btb/ClassicII/ClassicIIRevB/ClassicIIRevB.kicad_sch

## KiCad design ClassicIIRevB/ClassicIIRevB.kicad_sch (2026-08-08)

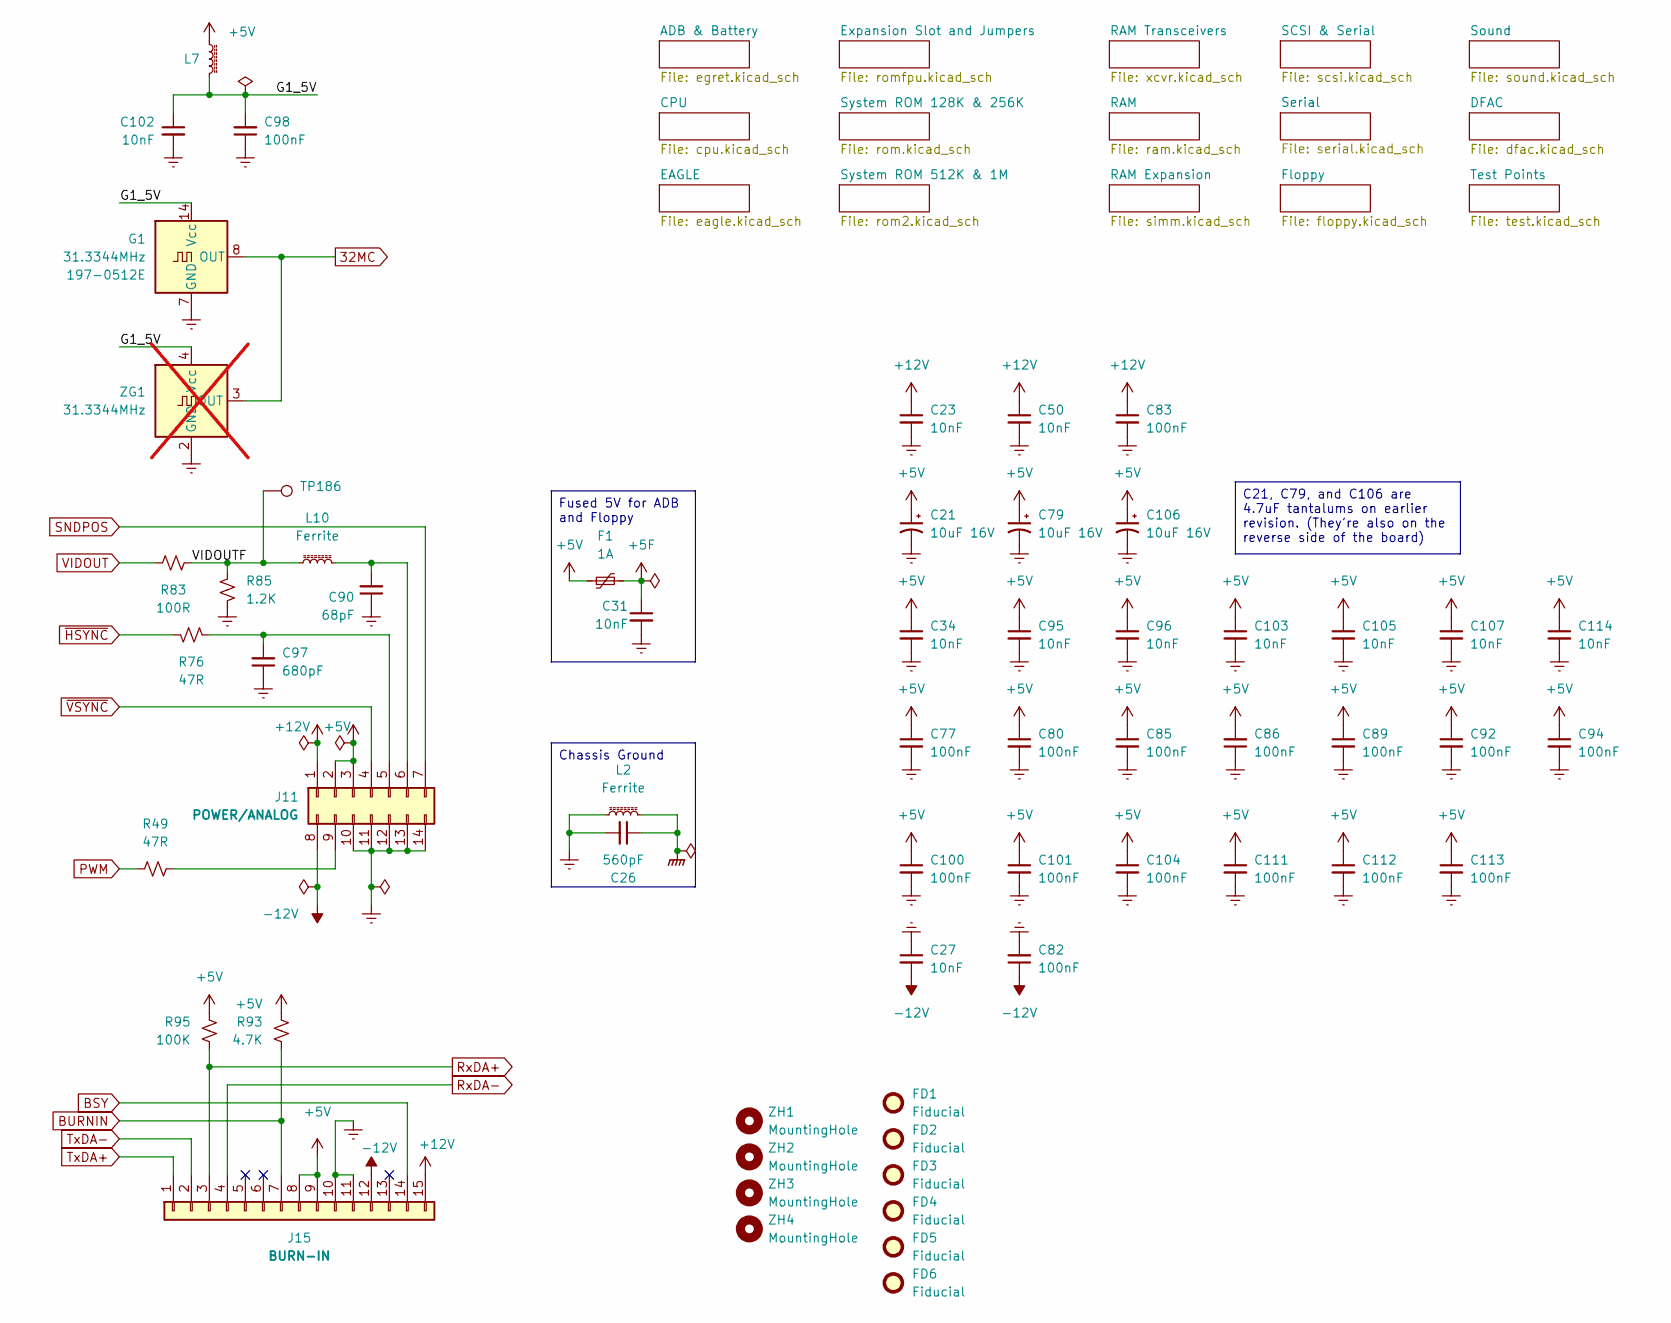
[picture p18: schematic ClassicIIRevB.kicad_sch]

Parts:
C21, C79, C106: 10uF 16V; CP_Elec_4x5.8
C23, C27, C31, C34, C50, C95, C96, C102, C103, C105, C107, C114: 10nF; SMD_0603_1608Metric_Pad1.52x1.02mm
C26: 560pF; SMD_0603_1608Metric_Pad1.52x1.02mm
C77, C80, C82, C83, C85, C86, C89, C92, C94, C98, C100, C101, C104, C113: 100nF; SMD_0603_1608Metric_Pad1.52x1.02mm
C90: 68pF; SMD_0603_1608Metric_Pad1.52x1.02mm
C97: 680pF; SMD_1206_3216Metric_Pad1.65x1.27mm
C111, C112: 100nF; SMD_0805_2012Metric_Pad1.25x1.65mm
F1: 1A; Fuse_2512_6332Metric_Pad2.54x2.54mm_HandSolder
FD1, FD6: Fiducial; Fiducial_1mm_Mask3mm_square
FD2, FD3, FD4, FD5: Fiducial; Fiducial_1mm_Mask3mm
G1: 31.3344MHz; Oscillator_DIP-14; PartNum 197-0512E
J11: POWER/ANALOG; Molex_Mini-Fit_Jr_5566-14A_2x07_P4.20mm_Vertical_RoundPads
J15: BURN-IN; Mac_Burn_In
L2, L7, L10: Ferrite; L_2010_5025Metric_Pad2.0x2.2mm_HandSolder
R49, R76: 47R; SMD_0805_2012Metric_Pad1.25x1.65mm
R83: 100R; SMD_0805_2012Metric_Pad1.25x1.65mm
R85: 1.2K; SMD_0805_2012Metric_Pad1.25x1.65mm
R93: 4.7K; SMD_0805_2012Metric_Pad1.25x1.65mm
R95: 100K; SMD_0805_2012Metric_Pad1.25x1.65mm
TP186: TestPoint_THTPad_D1.0mm_Drill0.5mm
ZG1: 31.3344MHz; Oscillator_SMD_Abracon_ABLNO; not fitted
ZH1, ZH2, ZH3, ZH4: MountingHole; MountingHole_3.2mm_M3_ISO14580

Connections:
32MC: G1.8 (OUT), ZG1.3 (OUT)
+5F: C31.1, F1.2
+5V: C21.1, C34.1, C77.1, C79.1, C80.1, C85.1, C86.2, C89.1, C92.1, C94.1, C95.1, C96.1, C100.1, C101.1, C103.1, C104.1, C105.1, C106.1, C107.1, C111.1, C112.1, C113.1, C114.1, F1.1, J11.2, J11.3, J15.8, J15.9, L7.2, R93.1, R95.1
+12V: C23.1, C50.1, C83.1, J11.1, J15.15
-12V: C27.2, C82.1, J11.8, J15.12
BSY: J15.14
BURNIN: J15.7, R93.2
G1_5V: C98.2, C102.1, G1.14 (Vcc), L7.1, ZG1.4 (Vcc)
GND: C21.2, C23.2, C26.2, C27.1, C31.2, C34.2, C50.2, C77.2, C79.2, C80.2, C82.2, C83.2, C85.2, C86.1, C89.2, C90.1, C92.2, C94.2, C95.2, C96.2, C97.1, C98.1, C100.2, C101.2, C102.2, C103.2, C104.2, C105.2, C106.2, C107.2, C111.2, C112.2, C113.2, C114.2, G1.7 (GND), J11.10, J11.11, J11.12, J11.13, J11.14, J15.10, J15.11, L2.1, R85.2, ZG1.2 (GND)
GNDPWR: C26.1, L2.2
unnamed: C90.2, J11.6, L10.2
unnamed: C97.2, J11.5, R76.2
unnamed: J11.9, R49.2
PWM: R49.1
RxDA+: J15.3, R95.2
RxDA-: J15.4
SNDPOS: J11.7
TxDA+: J15.1
TxDA-: J15.2
VIDOUT: R83.1
VIDOUTF: L10.1, R83.2, R85.1, TP186.1
~HSYNC: R76.1
~VSYNC: J11.4

Notes on the sheet:
Fused 5V for ADB and Floppy
Chassis Ground
C21, C79, and C106 are 4.7uF tantalums on earlier revision. (They're also on the reverse side of the board)
