btb/ClassicII/ClassicIIRevB/cpu.kicad_sch

## KiCad design ClassicIIRevB/cpu.kicad_sch (2026-08-08)

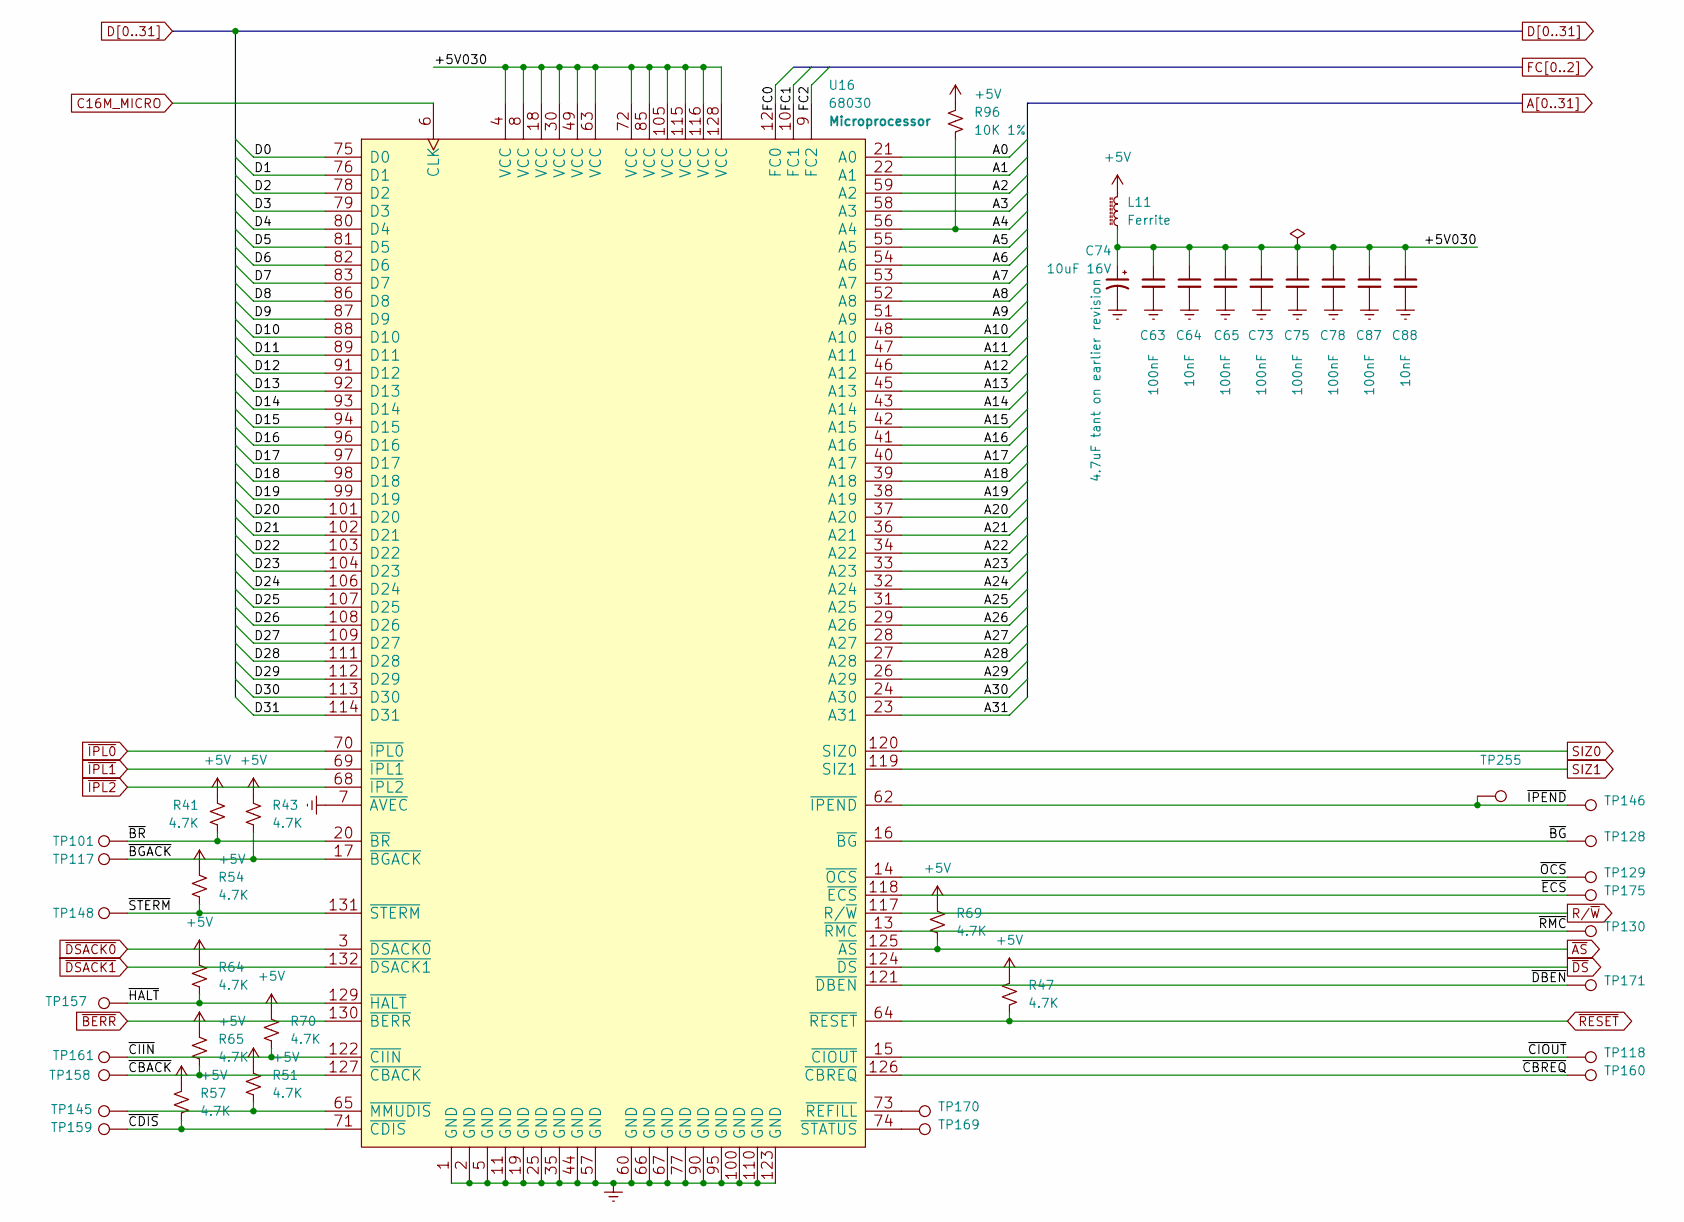
[picture p19: schematic cpu.kicad_sch]

Parts:
C63, C65, C73, C75, C78, C87: 100nF; SMD_0603_1608Metric_Pad1.52x1.02mm
C64, C88: 10nF; SMD_0603_1608Metric_Pad1.52x1.02mm
C74: 10uF 16V; CP_Elec_4x5.8
L11: Ferrite; L_2010_5025Metric_Pad2.0x2.2mm_HandSolder
R41, R43, R47, R51, R54, R57, R64, R65, R69, R70: 4.7K; SMD_0805_2012Metric_Pad1.25x1.65mm
R96: 10K 1%; SMD_0805_2012Metric_Pad1.25x1.65mm
TP101, TP117, TP118, TP128, TP129, TP130, TP145, TP146, TP148, TP159, TP169, TP170, TP171, TP255: TestPoint_THTPad_D1.0mm_Drill0.5mm
TP157, TP158, TP160, TP161, TP175: TestPoint_Pad_D1.0mm
U16: 68030; PQFP-132_24x24mm_P0.635mm_alt

Connections:
+5V: L11.1, R41.1, R43.1, R47.1, R51.1, R54.1, R57.1, R64.1, R65.1, R69.1, R70.1, R96.2
+5V030: C63.1, C64.1, C65.1, C73.1, C74.1, C75.1, C78.1, C87.1, C88.1, L11.2, U16.4 (VCC), U16.8 (VCC), U16.18 (VCC), U16.30 (VCC), U16.49 (VCC), U16.63 (VCC), U16.72 (VCC), U16.85 (VCC), U16.105 (VCC), U16.115 (VCC), U16.116 (VCC), U16.128 (VCC)
A0: U16.21 (A0)
A1: U16.22 (A1)
A2: U16.59 (A2)
A3: U16.58 (A3)
A4: R96.1, U16.56 (A4)
A5: U16.55 (A5)
A6: U16.54 (A6)
A7: U16.53 (A7)
A8: U16.52 (A8)
A9: U16.51 (A9)
A10: U16.48 (A10)
A11: U16.47 (A11)
A12: U16.46 (A12)
A13: U16.45 (A13)
A14: U16.43 (A14)
A15: U16.42 (A15)
A16: U16.41 (A16)
A17: U16.40 (A17)
A18: U16.39 (A18)
A19: U16.38 (A19)
A20: U16.37 (A20)
A21: U16.36 (A21)
A22: U16.34 (A22)
A23: U16.33 (A23)
A24: U16.32 (A24)
A25: U16.31 (A25)
A26: U16.29 (A26)
A27: U16.28 (A27)
A28: U16.27 (A28)
A29: U16.26 (A29)
A30: U16.24 (A30)
A31: U16.23 (A31)
C16M_MICRO: U16.6 (CLK)
D0: U16.75 (D0)
D1: U16.76 (D1)
D2: U16.78 (D2)
D3: U16.79 (D3)
D4: U16.80 (D4)
D5: U16.81 (D5)
D6: U16.82 (D6)
D7: U16.83 (D7)
D8: U16.86 (D8)
D9: U16.87 (D9)
D10: U16.88 (D10)
D11: U16.89 (D11)
D12: U16.91 (D12)
D13: U16.92 (D13)
D14: U16.93 (D14)
D15: U16.94 (D15)
D16: U16.96 (D16)
D17: U16.97 (D17)
D18: U16.98 (D18)
D19: U16.99 (D19)
D20: U16.101 (D20)
D21: U16.102 (D21)
D22: U16.103 (D22)
D23: U16.104 (D23)
D24: U16.106 (D24)
D25: U16.107 (D25)
D26: U16.108 (D26)
D27: U16.109 (D27)
D28: U16.111 (D28)
D29: U16.112 (D29)
D30: U16.113 (D30)
D31: U16.114 (D31)
FC0: U16.12 (FC0)
FC1: U16.10 (FC1)
FC2: U16.9 (FC2)
GND: C63.2, C64.2, C65.2, C73.2, C74.2, C75.2, C78.2, C87.2, C88.2, U16.1 (GND), U16.2 (GND), U16.5 (GND), U16.7 (~AVEC), U16.11 (GND), U16.19 (GND), U16.25 (GND), U16.35 (GND), U16.44 (GND), U16.57 (GND), U16.60 (GND), U16.66 (GND), U16.67 (GND), U16.77 (GND), U16.90 (GND), U16.95 (GND), U16.100 (GND), U16.110 (GND), U16.123 (GND)
unnamed: R51.2, TP145.1, U16.65 (~MMUDIS)
unnamed: TP169.1, U16.74 (~STATUS)
unnamed: TP170.1, U16.73 (~REFILL)
R/~W: U16.117 (R/~W)
SIZ0: U16.120 (SIZ0)
SIZ1: U16.119 (SIZ1)
~AS: R69.2, U16.125 (~AS)
~BERR: U16.130 (~BERR)
~BGACK: R43.2, TP117.1, U16.17 (~BGACK)
~BG: TP128.1, U16.16 (~BG)
~BR: R41.2, TP101.1, U16.20 (~BR)
~CBACK: R65.2, TP158.1, U16.127 (~CBACK)
~CBREQ: TP160.1, U16.126 (~CBREQ)
~CDIS: R57.2, TP159.1, U16.71 (~CDIS)
~CIIN: R70.2, TP161.1, U16.122 (~CIIN)
~CIOUT: TP118.1, U16.15 (~CIOUT)
~DBEN: TP171.1, U16.121 (~DBEN)
~DSACK0: U16.3 (~DSACK0)
~DSACK1: U16.132 (~DSACK1)
~DS: U16.124 (~DS)
~ECS: TP175.1, U16.118 (~ECS)
~HALT: R64.2, TP157.1, U16.129 (~HALT)
~IPEND: TP146.1, TP255.1, U16.62 (~IPEND)
~IPL0: U16.70 (~IPL0)
~IPL1: U16.69 (~IPL1)
~IPL2: U16.68 (~IPL2)
~OCS: TP129.1, U16.14 (~OCS)
~RESET: R47.2, U16.64 (~RESET)
~RMC: TP130.1, U16.13 (~RMC)
~STERM: R54.2, TP148.1, U16.131 (~STERM)
