btb/ClassicII/ClassicIIRevB/dfac.kicad_sch

## KiCad design ClassicIIRevB/dfac.kicad_sch (2026-08-08)

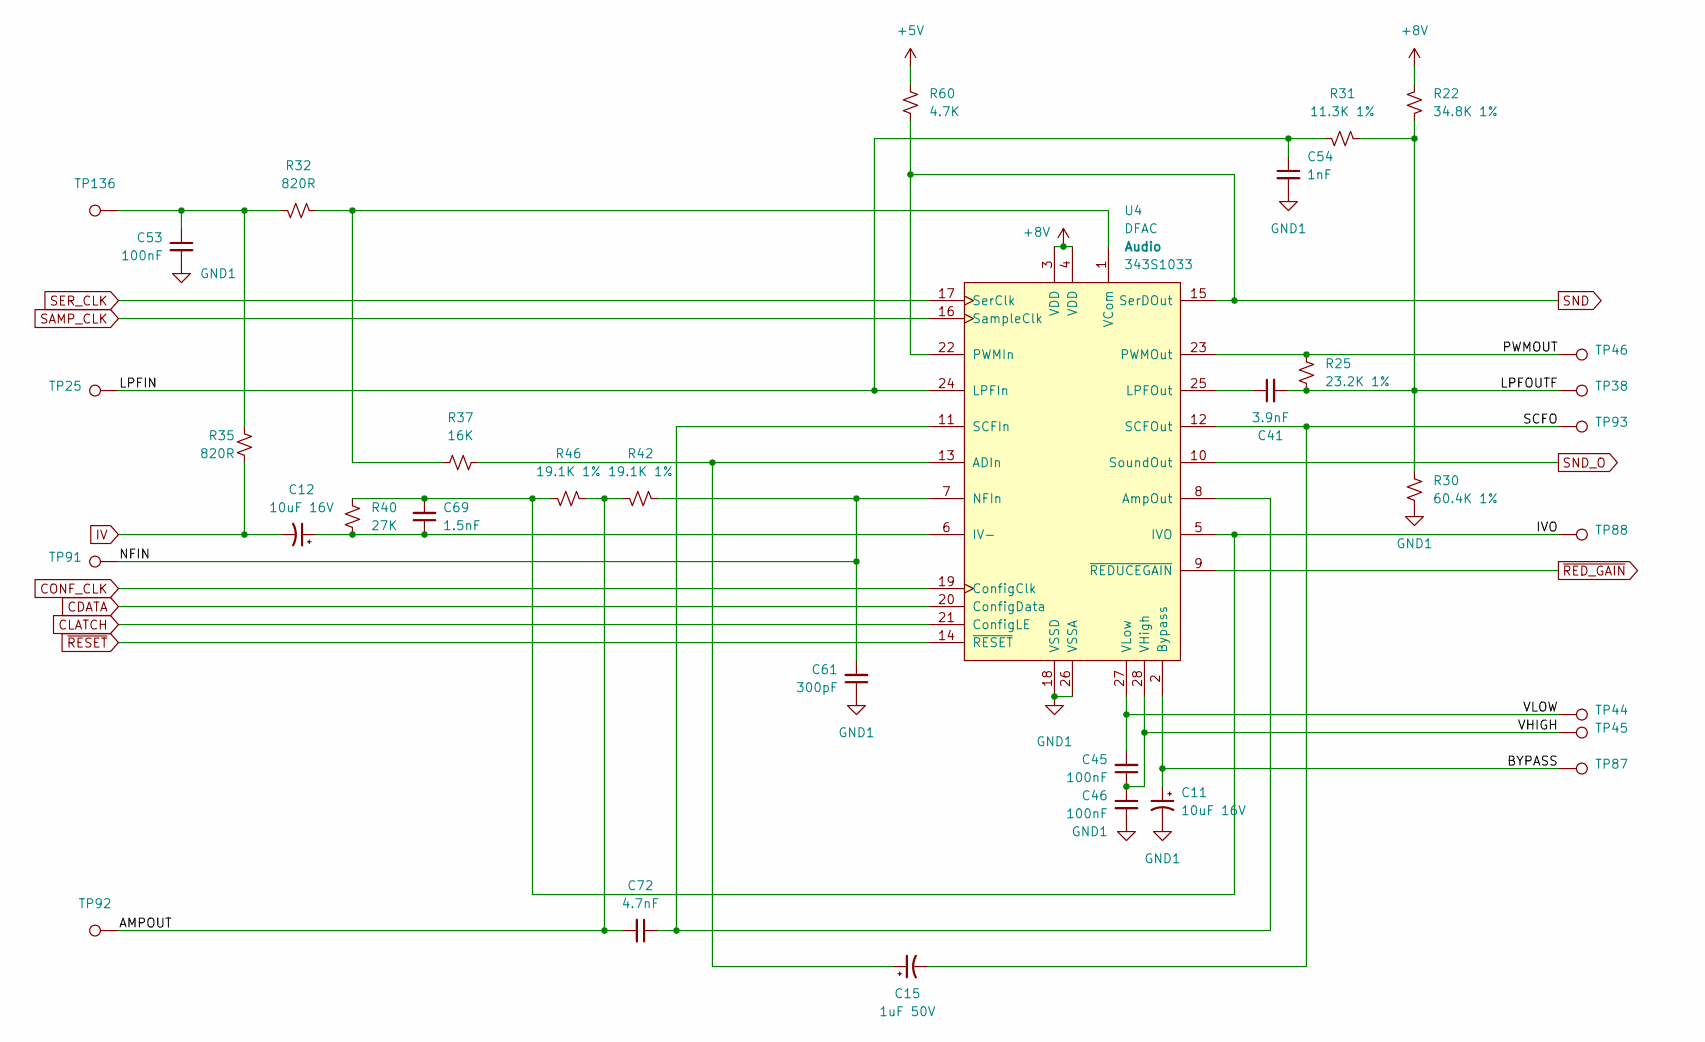
[picture p20: schematic dfac.kicad_sch]

Parts:
C11, C12: 10uF 16V; CP_Elec_4x5.8
C15: 1uF 50V; CP_Elec_4x5.8
C41: 3.9nF; SMD_0603_1608Metric_Pad1.52x1.02mm
C45, C46, C53: 100nF; SMD_0603_1608Metric_Pad1.52x1.02mm
C54: 1nF; SMD_0603_1608Metric_Pad1.52x1.02mm
C61: 300pF; SMD_1206_3216Metric_Pad1.65x1.27mm
C69: 1.5nF; SMD_0805_2012Metric_Pad1.25x1.65mm
C72: 4.7nF; SMD_0603_1608Metric_Pad1.52x1.02mm
R22: 34.8K 1%; SMD_0805_2012Metric_Pad1.25x1.65mm
R25: 23.2K 1%; SMD_0805_2012Metric_Pad1.25x1.65mm
R30: 60.4K 1%; SMD_0805_2012Metric_Pad1.25x1.65mm
R31: 11.3K 1%; SMD_0805_2012Metric_Pad1.25x1.65mm
R32, R35: 820R; SMD_0805_2012Metric_Pad1.25x1.65mm
R37: 16K; SMD_0805_2012Metric_Pad1.25x1.65mm
R40: 27K; SMD_0805_2012Metric_Pad1.25x1.65mm
R42, R46: 19.1K 1%; SMD_0805_2012Metric_Pad1.25x1.65mm
R60: 4.7K; SMD_0805_2012Metric_Pad1.25x1.65mm
TP25, TP44, TP87, TP93: TestPoint_THTPad_D1.0mm_Drill0.5mm
TP38, TP45, TP46, TP88, TP91, TP92, TP136: TestPoint_Pad_D1.0mm
U4: DFAC; PLCC-28_rounded; PartNum 343S1033

Connections:
+5V: R60.1
+8V: R22.1, U4.3 (VDD), U4.4 (VDD)
AMPOUT: C72.2, R42.1, R46.1, TP92.1
BYPASS: C11.1, TP87.1, U4.2 (Bypass)
CDATA: U4.20 (ConfigData)
CLATCH: U4.21 (ConfigLE)
CONF_CLK: U4.19 (ConfigClk)
GND1: C11.2, C46.2, C53.2, C54.2, C61.1, R30.1, U4.18 (VSSD), U4.26 (VSSA)
IV: C12.2, R35.1
IVO: C69.2, R40.1, R46.2, TP88.1, U4.5 (IVO)
LPFIN: C54.1, R31.2, TP25.1, U4.24 (LPFIn)
LPFOUTF: C41.2, R22.2, R25.1, R30.2, R31.1, TP38.1
NFIN: C61.2, R42.2, TP91.1, U4.7 (NFIn)
unnamed: C12.1, C69.1, R40.2, U4.6 (IV-)
unnamed: C15.1, R37.1, U4.13 (ADIn)
unnamed: C41.1, U4.25 (LPFOut)
unnamed: C53.1, R32.1, R35.2, TP136.1
unnamed: C72.1, U4.8 (AmpOut), U4.11 (SCFIn)
unnamed: R32.2, R37.2, U4.1 (VCom)
PWMOUT: R25.2, TP46.1, U4.23 (PWMOut)
SAMP_CLK: U4.16 (SampleClk)
SCFO: C15.2, TP93.1, U4.12 (SCFOut)
SER_CLK: U4.17 (SerClk)
SND: R60.2, U4.15 (SerDOut), U4.22 (PWMIn)
SND_O: U4.10 (SoundOut)
VHIGH: C45.1, C46.1, TP45.1, U4.28 (VHigh)
VLOW: C45.2, TP44.1, U4.27 (VLow)
~RED_GAIN: U4.9 (~REDUCEGAIN)
~RESET: U4.14 (~RESET)
