btb/ClassicII/ClassicIIRevB/eagle.kicad_sch

## KiCad design ClassicIIRevB/eagle.kicad_sch (2026-08-08)

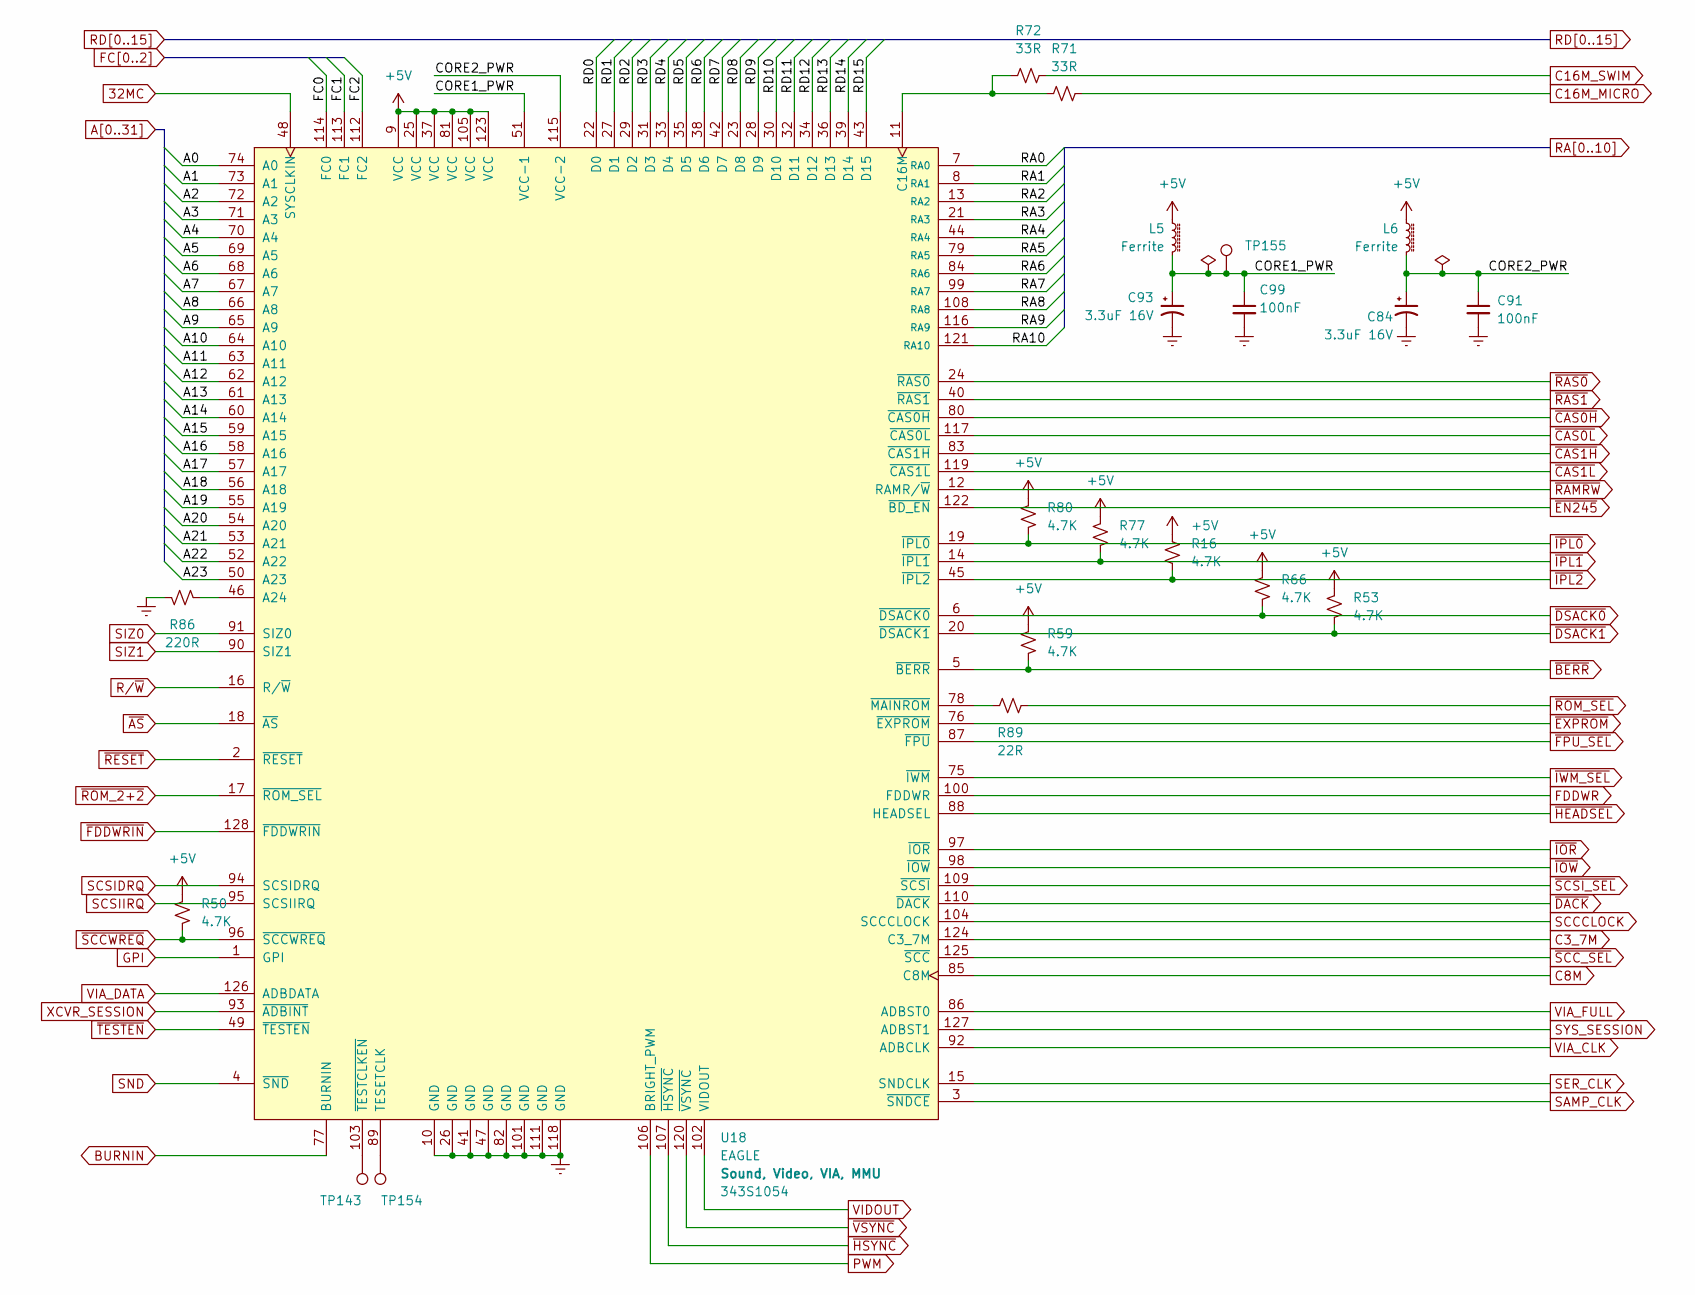
[picture p21: schematic eagle.kicad_sch]

Parts:
C84, C93: 3.3uF 16V; CP_EIA-3528-21_Kemet-B_Pad3.0x2.35mm_HandSolder
C91, C99: 100nF; SMD_0603_1608Metric_Pad1.52x1.02mm
L5, L6: Ferrite; L_2010_5025Metric_Pad2.0x2.2mm_HandSolder
R16, R50, R53, R59, R66, R77, R80: 4.7K; SMD_0805_2012Metric_Pad1.25x1.65mm
R71, R72: 33R; SMD_0805_2012Metric_Pad1.25x1.65mm
R86: 220R; SMD_0805_2012Metric_Pad1.25x1.65mm
R89: 22R; SMD_0805_2012Metric_Pad1.25x1.65mm
TP143, TP154, TP155: TestPoint_THTPad_D1.0mm_Drill0.5mm
U18: EAGLE; TQFP-128_28x28mm_P0.8mm; PartNum 343S1054

Connections:
32MC: U18.48 (SYSCLKIN)
+5V: L5.1, L6.1, R16.1, R50.1, R53.1, R59.1, R66.1, R77.2, R80.1, U18.9 (VCC), U18.25 (VCC), U18.37 (VCC), U18.81 (VCC), U18.105 (VCC), U18.123 (VCC)
A0: U18.74 (A0)
A1: U18.73 (A1)
A2: U18.72 (A2)
A3: U18.71 (A3)
A4: U18.70 (A4)
A5: U18.69 (A5)
A6: U18.68 (A6)
A7: U18.67 (A7)
A8: U18.66 (A8)
A9: U18.65 (A9)
A10: U18.64 (A10)
A11: U18.63 (A11)
A12: U18.62 (A12)
A13: U18.61 (A13)
A14: U18.60 (A14)
A15: U18.59 (A15)
A16: U18.58 (A16)
A17: U18.57 (A17)
A18: U18.56 (A18)
A19: U18.55 (A19)
A20: U18.54 (A20)
A21: U18.53 (A21)
A22: U18.52 (A22)
A23: U18.50 (A23)
BURNIN: U18.77 (BURNIN)
C3_7M: U18.124 (C3_7M)
C8M: U18.85 (C8M)
C16M_MICRO: R71.1
C16M_SWIM: R72.1
CORE1_PWR: C93.1, C99.1, L5.2, TP155.1, U18.51 (VCC-1)
CORE2_PWR: C84.1, C91.1, L6.2, U18.115 (VCC-2)
FC0: U18.114 (FC0)
FC1: U18.113 (FC1)
FC2: U18.112 (FC2)
FDDWR: U18.100 (FDDWR)
GND: C84.2, C91.2, C93.2, C99.2, R86.1, U18.10 (GND), U18.26 (GND), U18.41 (GND), U18.47 (GND), U18.82 (GND), U18.101 (GND), U18.111 (GND), U18.118 (GND)
GPI: U18.1 (GPI)
unnamed: R71.2, R72.2, U18.11 (C16M)
unnamed: R86.2, U18.46 (A24)
unnamed: R89.1, U18.78 (~MAINROM)
unnamed: TP143.1, U18.103 (~TESTCLKEN)
unnamed: TP154.1, U18.89 (TESETCLK)
PWM: U18.106 (BRIGHT_PWM)
RA0: U18.7 (RA0)
RA1: U18.8 (RA1)
RA2: U18.13 (RA2)
RA3: U18.21 (RA3)
RA4: U18.44 (RA4)
RA5: U18.79 (RA5)
RA6: U18.84 (RA6)
RA7: U18.99 (RA7)
RA8: U18.108 (RA8)
RA9: U18.116 (RA9)
RA10: U18.121 (RA10)
RD0: U18.22 (D0)
RD1: U18.27 (D1)
RD2: U18.29 (D2)
RD3: U18.31 (D3)
RD4: U18.33 (D4)
RD5: U18.35 (D5)
RD6: U18.38 (D6)
RD7: U18.42 (D7)
RD8: U18.23 (D8)
RD9: U18.28 (D9)
RD10: U18.30 (D10)
RD11: U18.32 (D11)
RD12: U18.34 (D12)
RD13: U18.36 (D13)
RD14: U18.39 (D14)
RD15: U18.43 (D15)
R/~W: U18.16 (R/~W)
SAMP_CLK: U18.3 (~SNDCE)
SCCCLOCK: U18.104 (SCCCLOCK)
SCSIDRQ: U18.94 (SCSIDRQ)
SCSIIRQ: U18.95 (SCSIIRQ)
SER_CLK: U18.15 (SNDCLK)
SIZ0: U18.91 (SIZ0)
SIZ1: U18.90 (SIZ1)
SND: U18.4 (~SND)
SYS_SESSION: U18.127 (ADBST1)
VIA_CLK: U18.92 (ADBCLK)
VIA_DATA: U18.126 (ADBDATA)
VIA_FULL: U18.86 (ADBST0)
VIDOUT: U18.102 (VIDOUT)
XCVR_SESSION: U18.93 (~ADBINT)
~AS: U18.18 (~AS)
~BERR: R59.2, U18.5 (~BERR)
~CAS0H: U18.80 (~CAS0H)
~CAS0L: U18.117 (~CAS0L)
~CAS1H: U18.83 (~CAS1H)
~CAS1L: U18.119 (~CAS1L)
~DACK: U18.110 (~DACK)
~DSACK0: R66.2, U18.6 (~DSACK0)
~DSACK1: R53.2, U18.20 (~DSACK1)
~EN245: U18.122 (~BD_EN)
~EXPROM: U18.76 (~EXPROM)
~FDDWRIN: U18.128 (~FDDWRIN)
~FPU_SEL: U18.87 (~FPU)
~HEADSEL: U18.88 (HEADSEL)
~HSYNC: U18.107 (~HSYNC)
~IOR: U18.97 (~IOR)
~IOW: U18.98 (~IOW)
~IPL0: R80.2, U18.19 (~IPL0)
~IPL1: R77.1, U18.14 (~IPL1)
~IPL2: R16.2, U18.45 (~IPL2)
~IWM_SEL: U18.75 (~IWM)
~RAMRW: U18.12 (RAMR/~W)
~RAS0: U18.24 (~RAS0)
~RAS1: U18.40 (~RAS1)
~RESET: U18.2 (~RESET)
~ROM_2+2: U18.17 (~ROM_SEL)
~ROM_SEL: R89.2
~SCCWREQ: R50.2, U18.96 (~SCCWREQ)
~SCC_SEL: U18.125 (~SCC)
~SCSI_SEL: U18.109 (~SCSI)
~TESTEN: U18.49 (~TESTEN)
~VSYNC: U18.120 (~VSYNC)
