btb/ClassicII/ClassicIIRevB/egret.kicad_sch

## KiCad design ClassicIIRevB/egret.kicad_sch (2026-08-08)

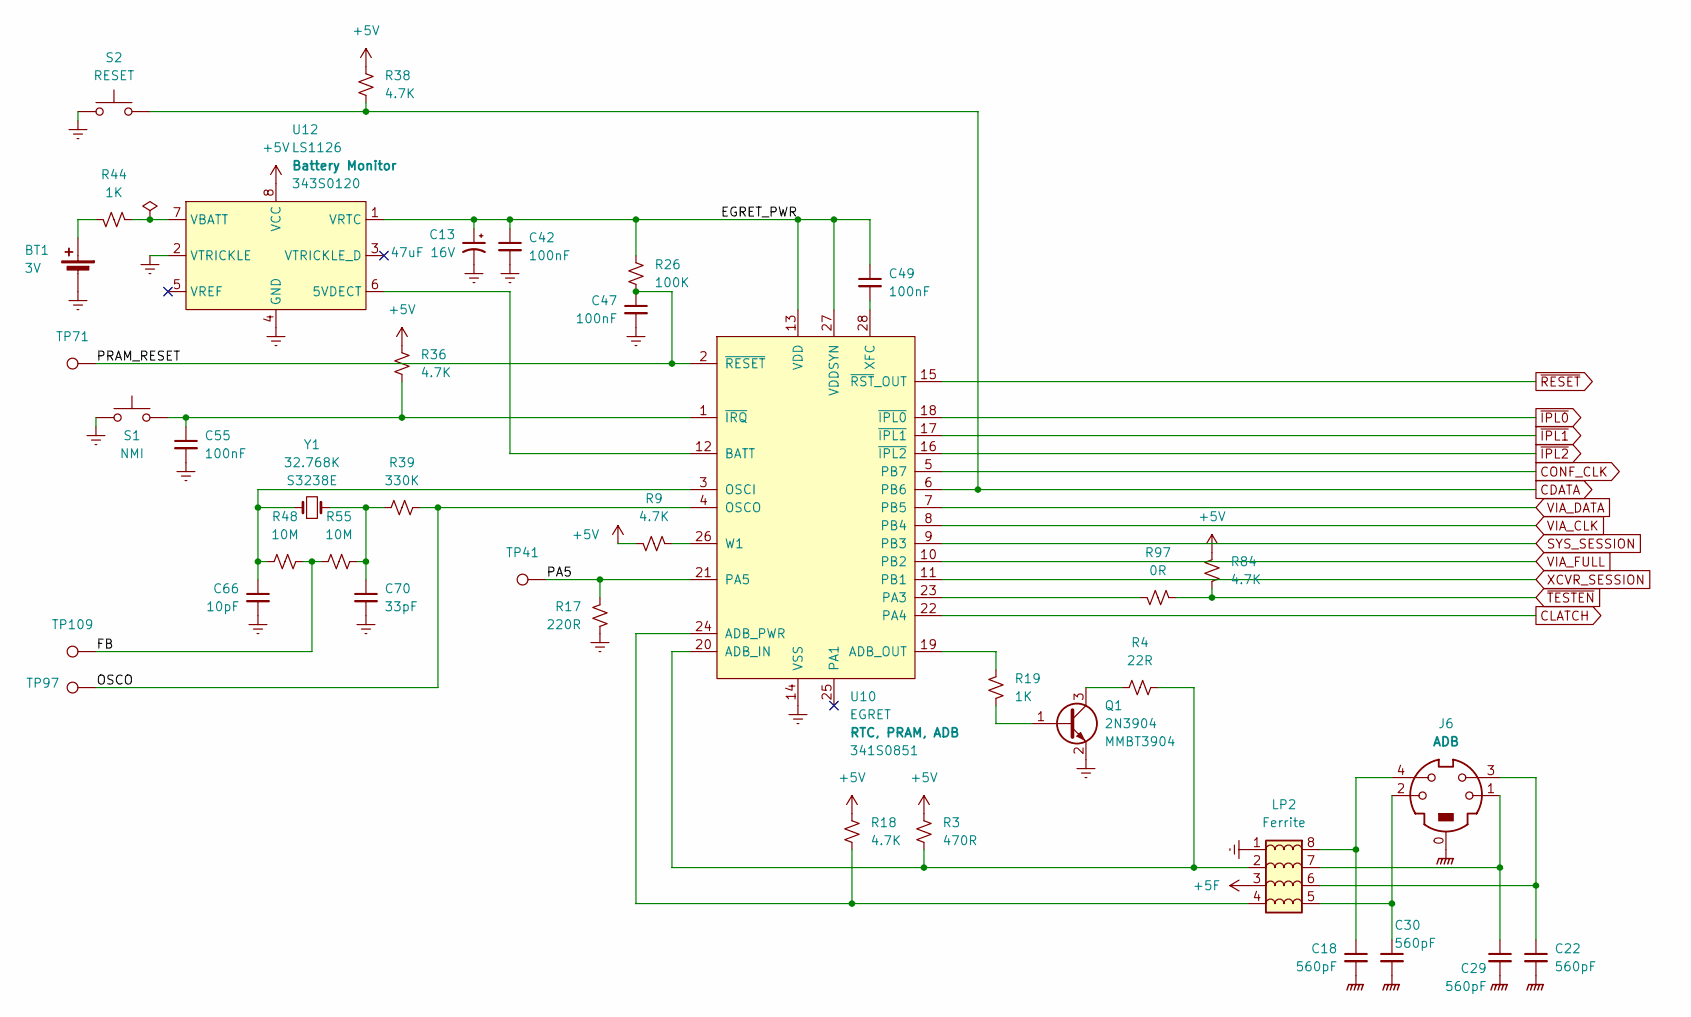
[picture p22: schematic egret.kicad_sch]

Parts:
BT1: 3V; BatteryHolder_Keystone_108_1_2xAA
C13: 47uF 16V; CP_Elec_6.3x5.4
C18, C22, C29, C30: 560pF; SMD_0603_1608Metric_Pad1.52x1.02mm
C42, C47, C49, C55: 100nF; SMD_0603_1608Metric_Pad1.52x1.02mm
C66: 10pF; SMD_0603_1608Metric_Pad1.52x1.02mm
C70: 33pF; SMD_0603_1608Metric_Pad1.52x1.02mm
J6: ADB; TE_5749263-1_MINI_DIN_4_RA_Shield
LP2: Ferrite; L_Pack04_P2.54mm
Q1: 2N3904; SOT-23_Handsoldering; PartNum MMBT3904
R3: 470R; SMD_0805_2012Metric_Pad1.25x1.65mm
R4: 22R; SMD_0805_2012Metric_Pad1.25x1.65mm
R9, R18, R36, R38, R84: 4.7K; SMD_0805_2012Metric_Pad1.25x1.65mm
R17: 220R; SMD_0805_2012Metric_Pad1.25x1.65mm
R19, R44: 1K; SMD_0805_2012Metric_Pad1.25x1.65mm
R26: 100K; SMD_0805_2012Metric_Pad1.25x1.65mm
R39: 330K; SMD_0805_2012Metric_Pad1.25x1.65mm
R48, R55: 10M; SMD_0805_2012Metric_Pad1.25x1.65mm
R97: 0R; SMD_0805_2012Metric_Pad1.25x1.65mm
S1: NMI; SW_SPST_Omron_B3F_angled
S2: RESET; SW_SPST_Omron_B3F_angled
TP41, TP71, TP109: TestPoint_THTPad_D1.0mm_Drill0.5mm
TP97: TestPoint_Pad_D1.0mm
U10: EGRET; SOIC-28W_7.5x17.9mm_P1.27mm_oval; PartNum 341S0851
U12: LS1126; SOIC-8_3.9x4.9mm_P1.27mm_oval; PartNum 343S0120
Y1: 32.768K; Crystal_AT310_D3.0mm_L10.0mm_Vertical; PartNum S3238E

Connections:
+5F: LP2.3
+5V: R3.1, R9.1, R18.1, R36.1, R38.1, R84.1, U12.8 (VCC)
CDATA: R38.2, S2.2, U10.6 (PB6)
CLATCH: U10.22 (PA4)
CONF_CLK: U10.5 (PB7)
EGRET_PWR: C13.1, C42.1, C49.1, R26.1, U10.13 (VDD), U10.27 (VDDSYN), U12.1 (VRTC)
FB: R48.2, R55.1, TP109.1
GND: BT1.2 (-), C13.2, C42.2, C47.2, C55.2, C66.2, C70.2, LP2.1, Q1.2 (E), R17.2, S1.1, S2.1, U10.14 (VSS), U12.2 (VTRICKLE), U12.4 (GND)
GNDPWR: C18.2, C22.2, C29.2, C30.2, J6.0
unnamed: BT1.1 (+), R44.1
unnamed: C18.1, J6.4, LP2.8
unnamed: C22.1, J6.3, LP2.6
unnamed: C29.1, J6.1, LP2.7
unnamed: C30.1, J6.2, LP2.5
unnamed: C49.2, U10.28 (XFC)
unnamed: C55.1, R36.2, S1.2, U10.1 (~IRQ)
unnamed: C66.1, R48.1, U10.3 (OSCI), Y1.1
unnamed: C70.1, R39.1, R55.2, Y1.2
unnamed: LP2.2, R3.2, R4.1, U10.20 (ADB_IN)
unnamed: LP2.4, R18.2, U10.24 (ADB_PWR)
unnamed: Q1.1 (B), R19.2
unnamed: Q1.3 (C), R4.2
unnamed: R9.2, U10.26 (W1)
unnamed: R19.1, U10.19 (ADB_OUT)
unnamed: R44.2, U12.7 (VBATT)
unnamed: R97.1, U10.23 (PA3)
unnamed: U10.12 (BATT), U12.6 (5VDECT)
OSCO: R39.2, TP97.1, U10.4 (OSCO)
PA5: R17.1, TP41.1, U10.21 (PA5)
PRAM_RESET: C47.1, R26.2, TP71.1, U10.2 (~RESET)
SYS_SESSION: U10.9 (PB3)
VIA_CLK: U10.8 (PB4)
VIA_DATA: U10.7 (PB5)
VIA_FULL: U10.10 (PB2)
XCVR_SESSION: U10.11 (PB1)
~IPL0: U10.18 (~IPL0)
~IPL1: U10.17 (~IPL1)
~IPL2: U10.16 (~IPL2)
~RESET: U10.15 (~RST_OUT)
~TESTEN: R84.2, R97.2
