btb/ClassicII/ClassicIIRevB/floppy.kicad_sch

## KiCad design ClassicIIRevB/floppy.kicad_sch (2026-08-08)

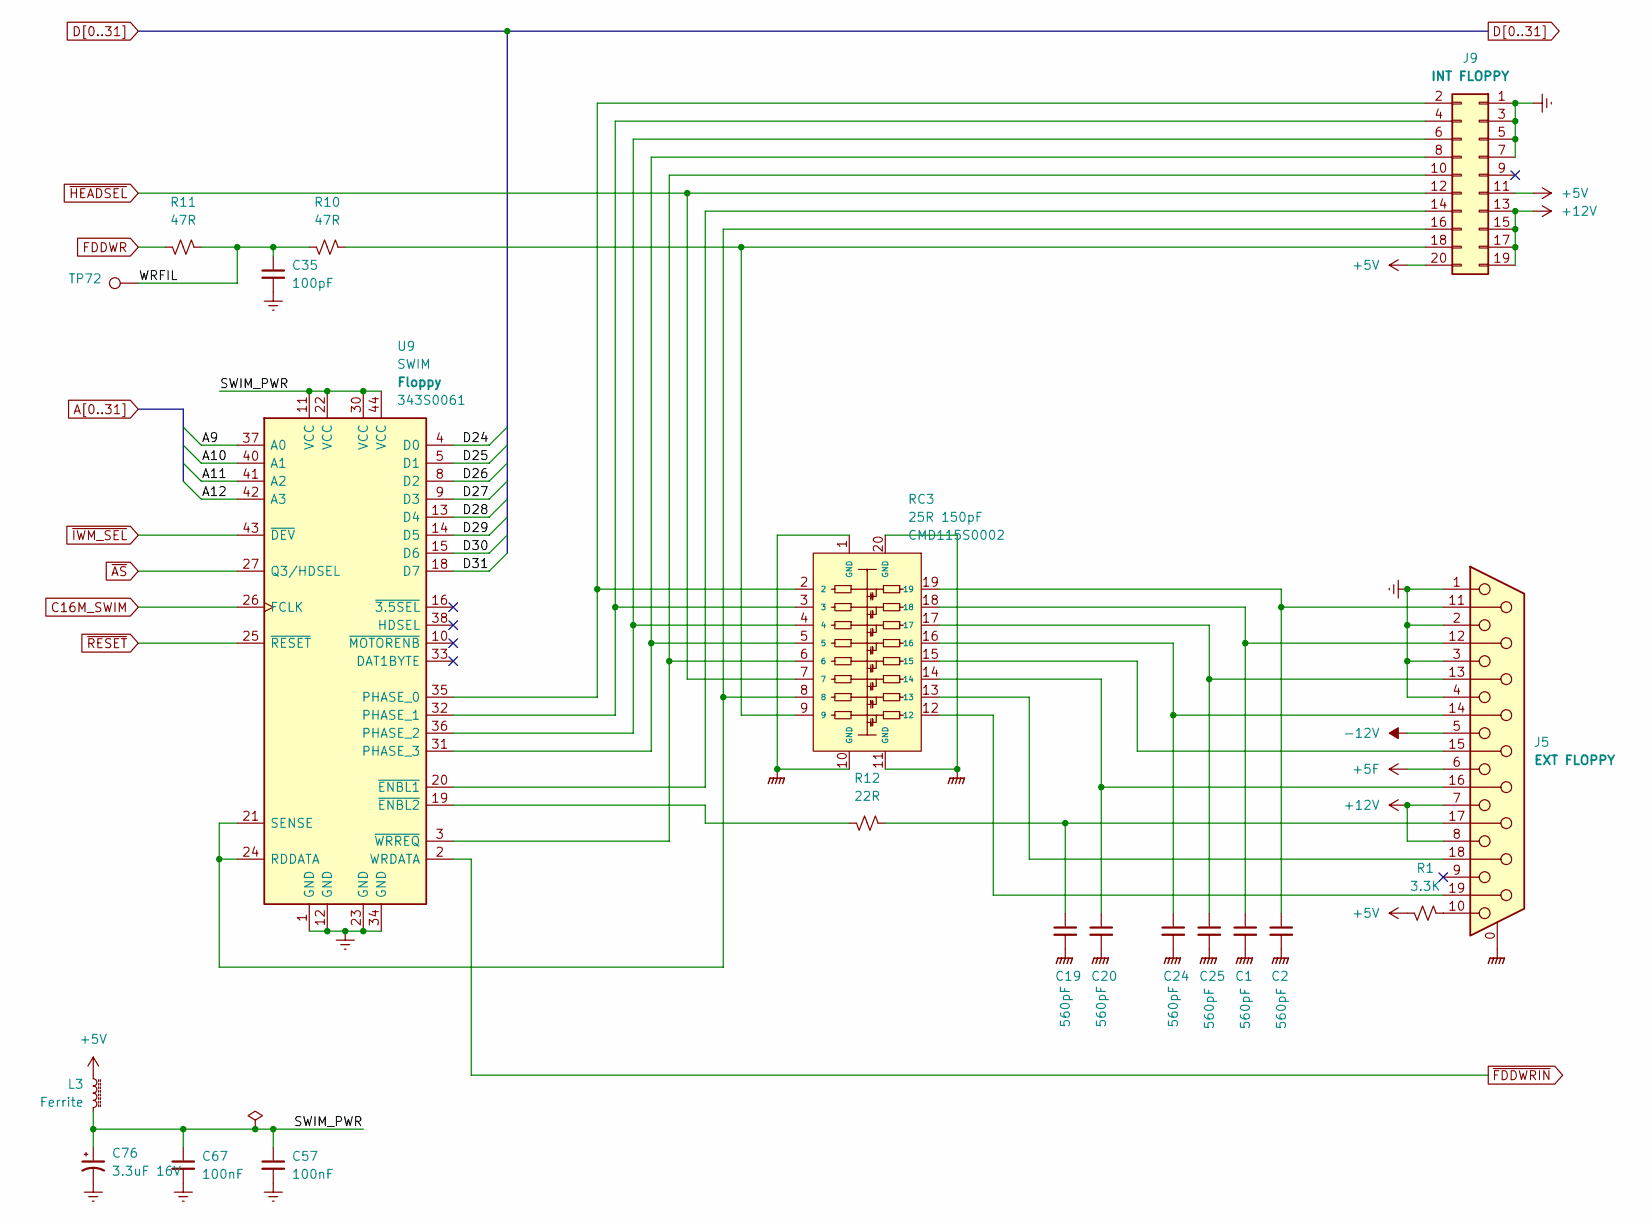
[picture p23: schematic floppy.kicad_sch]

Parts:
C1, C2, C19, C20, C24, C25: 560pF; SMD_0603_1608Metric_Pad1.52x1.02mm
C35: 100pF; SMD_0603_1608Metric_Pad1.52x1.02mm
C57, C67: 100nF; SMD_0603_1608Metric_Pad1.52x1.02mm
C76: 3.3uF 16V; CP_EIA-3528-21_Kemet-B_Pad3.0x2.35mm_HandSolder
J5: EXT FLOPPY; DSUB-19_Female_Horizontal_P2.77x2.84mm_EdgePinOffset4.94mm_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
J9: INT FLOPPY; IDC-Header_2x10_P2.54mm_Vertical
L3: Ferrite; L_2010_5025Metric_Pad2.0x2.2mm_HandSolder
R1: 3.3K; SMD_0805_2012Metric_Pad1.25x1.65mm
R10, R11: 47R; SMD_0805_2012Metric_Pad1.25x1.65mm
R12: 22R; SMD_0805_2012Metric_Pad1.25x1.65mm
RC3: 25R 150pF; SOIC-20W_7.5x12.8mm_P1.27mm_oval; PartNum CMD115S0002
TP72: TestPoint_Pad_D1.0mm
U9: SWIM; PLCC-44_16.6x16.6mm_P1.27mm_oval; PartNum 343S0061

Connections:
+5F: J5.6
+5V: J9.11, J9.20, L3.2, R1.1
+12V: J5.7, J5.8, J9.13, J9.15, J9.17, J9.19
-12V: J5.5
A9: U9.37 (A0)
A10: U9.40 (A1)
A11: U9.41 (A2)
A12: U9.42 (A3)
C16M_SWIM: U9.26 (FCLK)
D24: U9.4 (D0)
D25: U9.5 (D1)
D26: U9.8 (D2)
D27: U9.9 (D3)
D28: U9.13 (D4)
D29: U9.14 (D5)
D30: U9.15 (D6)
D31: U9.18 (D7)
FDDWR: R11.1
GND: C35.2, C57.2, C67.2, C76.2, J5.1, J5.2, J5.3, J5.4, J9.1, J9.3, J9.5, J9.7, U9.1 (GND), U9.12 (GND), U9.23 (GND), U9.34 (GND)
GNDPWR: C1.2, C2.2, C19.2, C20.2, C24.2, C25.2, J5.0 (PAD), RC3.1 (GND), RC3.10 (GND), RC3.11 (GND), RC3.20 (GND)
unnamed: C1.1, J5.12, RC3.18
unnamed: C2.1, J5.11, RC3.19
unnamed: C19.1, J5.17, R12.1
unnamed: C20.1, J5.16, RC3.14
unnamed: C24.1, J5.14, RC3.16
unnamed: C25.1, J5.13, RC3.17
unnamed: J5.10, R1.2
unnamed: J5.15, RC3.15
unnamed: J5.18, RC3.13
unnamed: J5.19, RC3.12
unnamed: J9.2, RC3.2, U9.35 (PHASE_0)
unnamed: J9.4, RC3.3, U9.32 (PHASE_1)
unnamed: J9.6, RC3.4, U9.36 (PHASE_2)
unnamed: J9.8, RC3.5, U9.31 (PHASE_3)
unnamed: J9.10, RC3.6, U9.3 (~WRREQ)
unnamed: J9.14, U9.20 (~ENBL1)
unnamed: J9.16, RC3.8, U9.21 (SENSE), U9.24 (RDDATA)
unnamed: J9.18, R10.2, RC3.9
unnamed: R12.2, U9.19 (~ENBL2)
SWIM_PWR: C57.1, C67.1, C76.1, L3.1, U9.11 (VCC), U9.22 (VCC), U9.30 (VCC), U9.44 (VCC)
WRFIL: C35.1, R10.1, R11.2, TP72.1
~AS: U9.27 (Q3/HDSEL)
~FDDWRIN: U9.2 (WRDATA)
~HEADSEL: J9.12, RC3.7
~IWM_SEL: U9.43 (~DEV)
~RESET: U9.25 (~RESET)
