btb/ClassicII/ClassicIIRevB/ram.kicad_sch

## KiCad design ClassicIIRevB/ram.kicad_sch (2026-08-08)

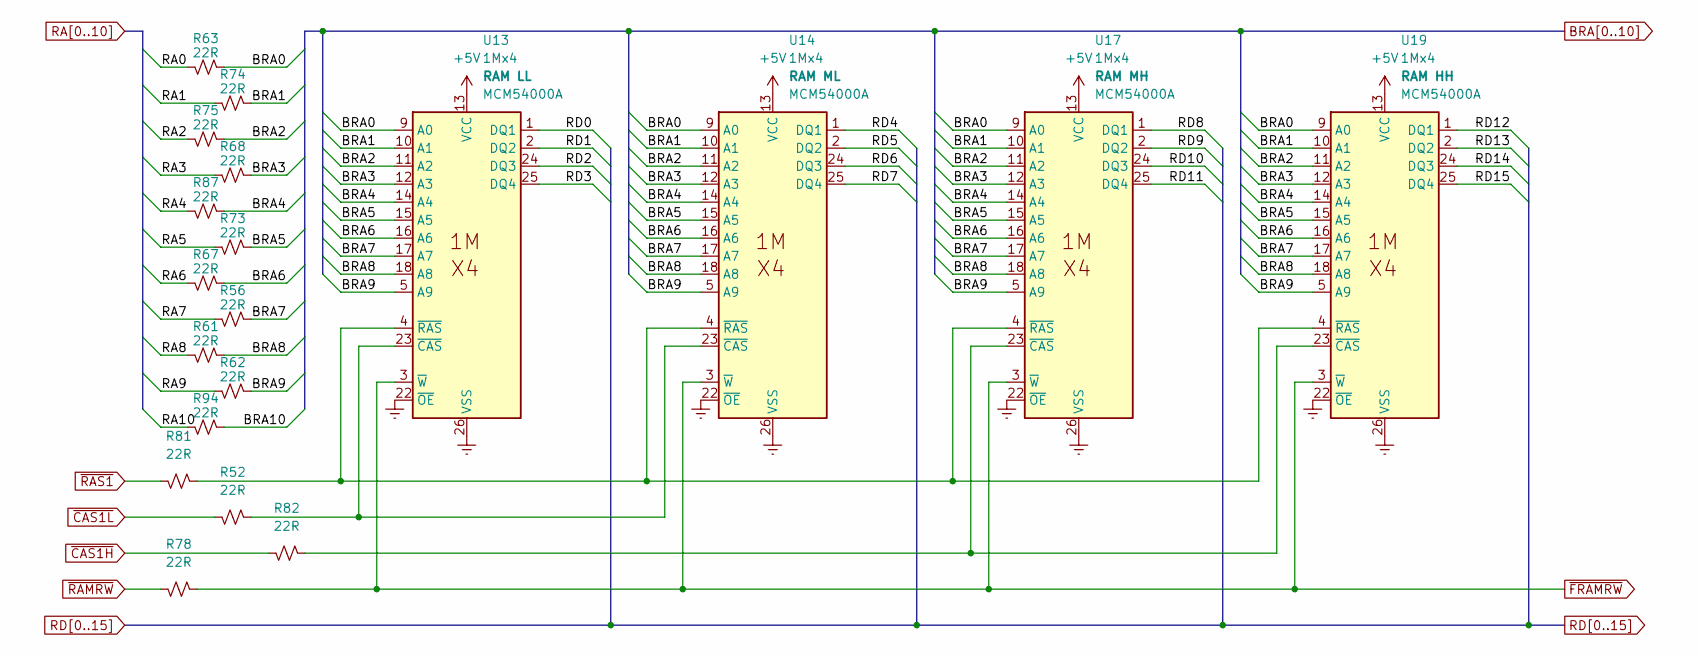
[picture p24: schematic ram.kicad_sch]

Parts:
R52, R56, R61, R62, R63, R67, R68, R73, R74, R75, R78, R81, R82, R87, R94: 22R; SMD_0805_2012Metric_Pad1.25x1.65mm
U13, U14, U17, U19: 1Mx4; SOJ-26-20_7.62x17.145mm_P1.27mm; PartNum MCM54000A

Connections:
+5V: U13.13 (VCC), U14.13 (VCC), U17.13 (VCC), U19.13 (VCC)
BRA0: R63.1, U13.9 (A0), U14.9 (A0), U17.9 (A0), U19.9 (A0)
BRA1: R74.1, U13.10 (A1), U14.10 (A1), U17.10 (A1), U19.10 (A1)
BRA2: R75.1, U13.11 (A2), U14.11 (A2), U17.11 (A2), U19.11 (A2)
BRA3: R68.1, U13.12 (A3), U14.12 (A3), U17.12 (A3), U19.12 (A3)
BRA4: R87.1, U13.14 (A4), U14.14 (A4), U17.14 (A4), U19.14 (A4)
BRA5: R73.2, U13.15 (A5), U14.15 (A5), U17.15 (A5), U19.15 (A5)
BRA6: R67.2, U13.16 (A6), U14.16 (A6), U17.16 (A6), U19.16 (A6)
BRA7: R56.2, U13.17 (A7), U14.17 (A7), U17.17 (A7), U19.17 (A7)
BRA8: R61.2, U13.18 (A8), U14.18 (A8), U17.18 (A8), U19.18 (A8)
BRA9: R62.2, U13.5 (A9), U14.5 (A9), U17.5 (A9), U19.5 (A9)
BRA10: R94.2
GND: U13.22 (~OE), U13.26 (VSS), U14.22 (~OE), U14.26 (VSS), U17.22 (~OE), U17.26 (VSS), U19.22 (~OE), U19.26 (VSS)
unnamed: R52.2, U13.23 (~CAS), U14.23 (~CAS)
unnamed: R81.1, U13.4 (~RAS), U14.4 (~RAS), U17.4 (~RAS), U19.4 (~RAS)
unnamed: R82.2, U17.23 (~CAS), U19.23 (~CAS)
RA0: R63.2
RA1: R74.2
RA2: R75.2
RA3: R68.2
RA4: R87.2
RA5: R73.1
RA6: R67.1
RA7: R56.1
RA8: R61.1
RA9: R62.1
RA10: R94.1
RD0: U13.1 (DQ1)
RD1: U13.2 (DQ2)
RD2: U13.24 (DQ3)
RD3: U13.25 (DQ4)
RD4: U14.1 (DQ1)
RD5: U14.2 (DQ2)
RD6: U14.24 (DQ3)
RD7: U14.25 (DQ4)
RD8: U17.1 (DQ1)
RD9: U17.2 (DQ2)
RD10: U17.24 (DQ3)
RD11: U17.25 (DQ4)
RD12: U19.1 (DQ1)
RD13: U19.2 (DQ2)
RD14: U19.24 (DQ3)
RD15: U19.25 (DQ4)
~CAS1H: R82.1
~CAS1L: R52.1
~FRAMRW: R78.1, U13.3 (~W), U14.3 (~W), U17.3 (~W), U19.3 (~W)
~RAMRW: R78.2
~RAS1: R81.2
