btb/ClassicII/ClassicIIRevB/rom2.kicad_sch

## KiCad design ClassicIIRevB/rom2.kicad_sch (2026-08-08)

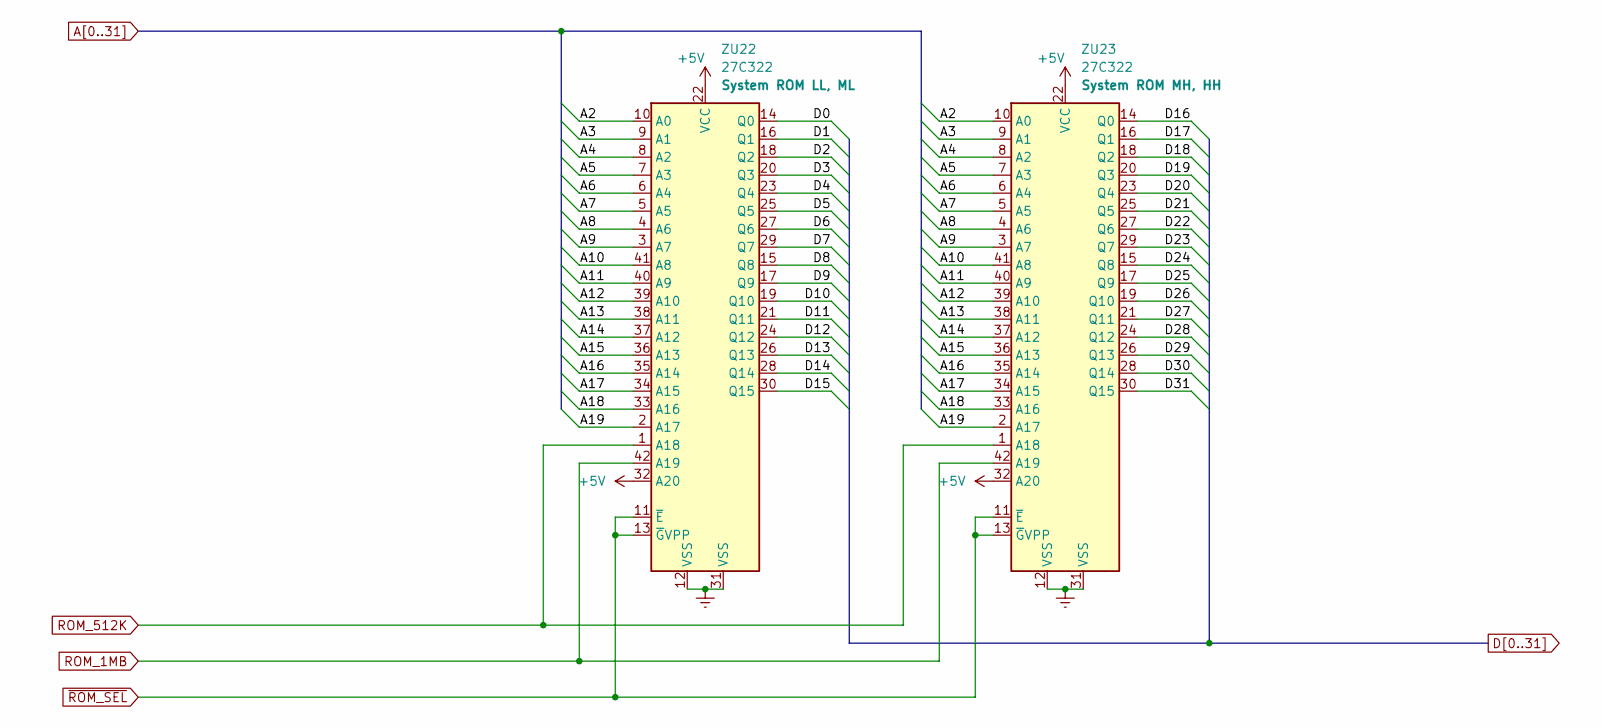
[picture p25: schematic rom2.kicad_sch]

Parts:
ZU22, ZU23: 27C322; DIP-42_W15.24mm_Socket

Connections:
+5V: ZU22.22 (VCC), ZU22.32 (A20), ZU23.22 (VCC), ZU23.32 (A20)
A2: ZU22.10 (A0), ZU23.10 (A0)
A3: ZU22.9 (A1), ZU23.9 (A1)
A4: ZU22.8 (A2), ZU23.8 (A2)
A5: ZU22.7 (A3), ZU23.7 (A3)
A6: ZU22.6 (A4), ZU23.6 (A4)
A7: ZU22.5 (A5), ZU23.5 (A5)
A8: ZU22.4 (A6), ZU23.4 (A6)
A9: ZU22.3 (A7), ZU23.3 (A7)
A10: ZU22.41 (A8), ZU23.41 (A8)
A11: ZU22.40 (A9), ZU23.40 (A9)
A12: ZU22.39 (A10), ZU23.39 (A10)
A13: ZU22.38 (A11), ZU23.38 (A11)
A14: ZU22.37 (A12), ZU23.37 (A12)
A15: ZU22.36 (A13), ZU23.36 (A13)
A16: ZU22.35 (A14), ZU23.35 (A14)
A17: ZU22.34 (A15), ZU23.34 (A15)
A18: ZU22.33 (A16), ZU23.33 (A16)
A19: ZU22.2 (A17), ZU23.2 (A17)
D0: ZU22.14 (Q0)
D1: ZU22.16 (Q1)
D2: ZU22.18 (Q2)
D3: ZU22.20 (Q3)
D4: ZU22.23 (Q4)
D5: ZU22.25 (Q5)
D6: ZU22.27 (Q6)
D7: ZU22.29 (Q7)
D8: ZU22.15 (Q8)
D9: ZU22.17 (Q9)
D10: ZU22.19 (Q10)
D11: ZU22.21 (Q11)
D12: ZU22.24 (Q12)
D13: ZU22.26 (Q13)
D14: ZU22.28 (Q14)
D15: ZU22.30 (Q15)
D16: ZU23.14 (Q0)
D17: ZU23.16 (Q1)
D18: ZU23.18 (Q2)
D19: ZU23.20 (Q3)
D20: ZU23.23 (Q4)
D21: ZU23.25 (Q5)
D22: ZU23.27 (Q6)
D23: ZU23.29 (Q7)
D24: ZU23.15 (Q8)
D25: ZU23.17 (Q9)
D26: ZU23.19 (Q10)
D27: ZU23.21 (Q11)
D28: ZU23.24 (Q12)
D29: ZU23.26 (Q13)
D30: ZU23.28 (Q14)
D31: ZU23.30 (Q15)
GND: ZU22.12 (VSS), ZU22.31 (VSS), ZU23.12 (VSS), ZU23.31 (VSS)
ROM_1MB: ZU22.42 (A19), ZU23.42 (A19)
ROM_512K: ZU22.1 (A18), ZU23.1 (A18)
~ROM_SEL: ZU22.11 (~E), ZU22.13 (~GVPP), ZU23.11 (~E), ZU23.13 (~GVPP)
