btb/ClassicII/ClassicIIRevB/rom.kicad_sch

## KiCad design ClassicIIRevB/rom.kicad_sch (2026-08-08)

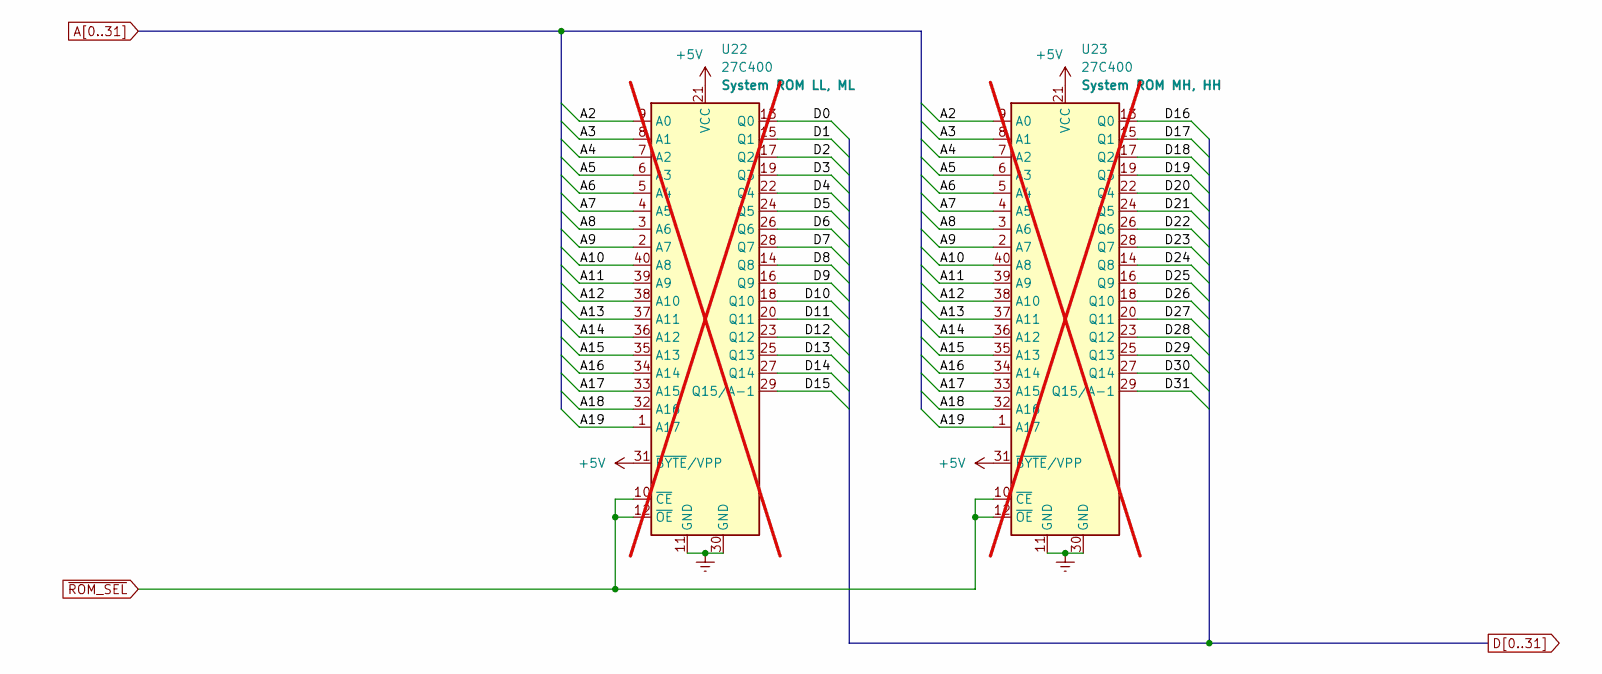
[picture p26: schematic rom.kicad_sch]

Parts:
U22, U23: 27C400; DIP-40_W15.24mm_Socket; not fitted

Connections:
+5V: U22.21 (VCC), U22.31 (~BYTE/VPP), U23.21 (VCC), U23.31 (~BYTE/VPP)
A2: U22.9 (A0), U23.9 (A0)
A3: U22.8 (A1), U23.8 (A1)
A4: U22.7 (A2), U23.7 (A2)
A5: U22.6 (A3), U23.6 (A3)
A6: U22.5 (A4), U23.5 (A4)
A7: U22.4 (A5), U23.4 (A5)
A8: U22.3 (A6), U23.3 (A6)
A9: U22.2 (A7), U23.2 (A7)
A10: U22.40 (A8), U23.40 (A8)
A11: U22.39 (A9), U23.39 (A9)
A12: U22.38 (A10), U23.38 (A10)
A13: U22.37 (A11), U23.37 (A11)
A14: U22.36 (A12), U23.36 (A12)
A15: U22.35 (A13), U23.35 (A13)
A16: U22.34 (A14), U23.34 (A14)
A17: U22.33 (A15), U23.33 (A15)
A18: U22.32 (A16), U23.32 (A16)
A19: U22.1 (A17), U23.1 (A17)
D0: U22.13 (Q0)
D1: U22.15 (Q1)
D2: U22.17 (Q2)
D3: U22.19 (Q3)
D4: U22.22 (Q4)
D5: U22.24 (Q5)
D6: U22.26 (Q6)
D7: U22.28 (Q7)
D8: U22.14 (Q8)
D9: U22.16 (Q9)
D10: U22.18 (Q10)
D11: U22.20 (Q11)
D12: U22.23 (Q12)
D13: U22.25 (Q13)
D14: U22.27 (Q14)
D15: U22.29 (Q15/A-1)
D16: U23.13 (Q0)
D17: U23.15 (Q1)
D18: U23.17 (Q2)
D19: U23.19 (Q3)
D20: U23.22 (Q4)
D21: U23.24 (Q5)
D22: U23.26 (Q6)
D23: U23.28 (Q7)
D24: U23.14 (Q8)
D25: U23.16 (Q9)
D26: U23.18 (Q10)
D27: U23.20 (Q11)
D28: U23.23 (Q12)
D29: U23.25 (Q13)
D30: U23.27 (Q14)
D31: U23.29 (Q15/A-1)
GND: U22.11 (GND), U22.30 (GND), U23.11 (GND), U23.30 (GND)
~ROM_SEL: U22.10 (~CE), U22.12 (~OE), U23.10 (~CE), U23.12 (~OE)
