btb/ClassicII/ClassicIIRevB/romfpu.kicad_sch

## KiCad design ClassicIIRevB/romfpu.kicad_sch (2026-08-08)

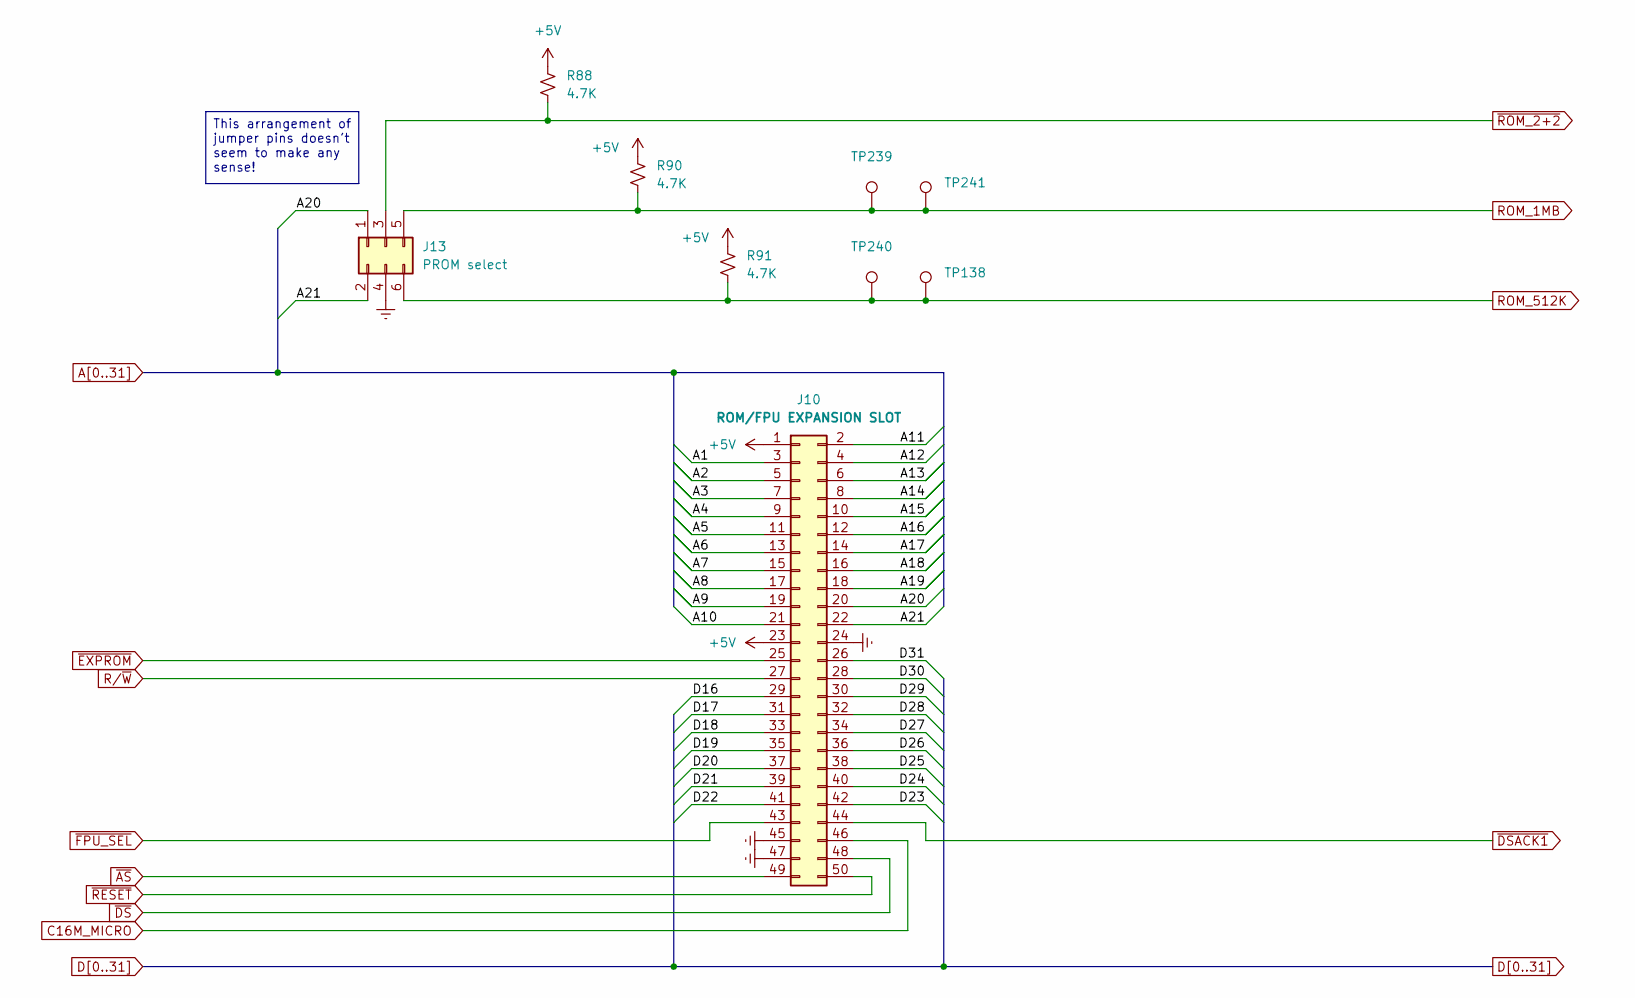
[picture p27: schematic romfpu.kicad_sch]

Parts:
J10: ROM/FPU EXPANSION SLOT; TE_5-102567-6
J13: PROM select; PinHeader_2x03_P2.54mm_Vertical
R88, R90, R91: 4.7K; SMD_0805_2012Metric_Pad1.25x1.65mm
TP138, TP239, TP240, TP241: TestPoint_THTPad_D1.0mm_Drill0.5mm

Connections:
+5V: J10.1, J10.23, R88.2, R90.2, R91.2
A1: J10.3
A2: J10.5
A3: J10.7
A4: J10.9
A5: J10.11
A6: J10.13
A7: J10.15
A8: J10.17
A9: J10.19
A10: J10.21
A11: J10.2
A12: J10.4
A13: J10.6
A14: J10.8
A15: J10.10
A16: J10.12
A17: J10.14
A18: J10.16
A19: J10.18
A20: J10.20, J13.1
A21: J10.22, J13.2
C16M_MICRO: J10.46
D16: J10.29
D17: J10.31
D18: J10.33
D19: J10.35
D20: J10.37
D21: J10.39
D22: J10.41
D23: J10.42
D24: J10.40
D25: J10.38
D26: J10.36
D27: J10.34
D28: J10.32
D29: J10.30
D30: J10.28
D31: J10.26
GND: J10.24, J10.45, J10.47, J13.4
ROM_1MB: J13.5, R90.1, TP239.1, TP241.1
ROM_512K: J13.6, R91.1, TP138.1, TP240.1
R/~W: J10.27
~AS: J10.49
~DSACK1: J10.44
~DS: J10.48
~EXPROM: J10.25
~FPU_SEL: J10.43
~RESET: J10.50
~ROM_2+2: J13.3, R88.1

Notes on the sheet:
This arrangement of jumper pins doesn't seem to make any sense!
