btb/ClassicII/ClassicIIRevB/scsi.kicad_sch

## KiCad design ClassicIIRevB/scsi.kicad_sch (2026-08-08)

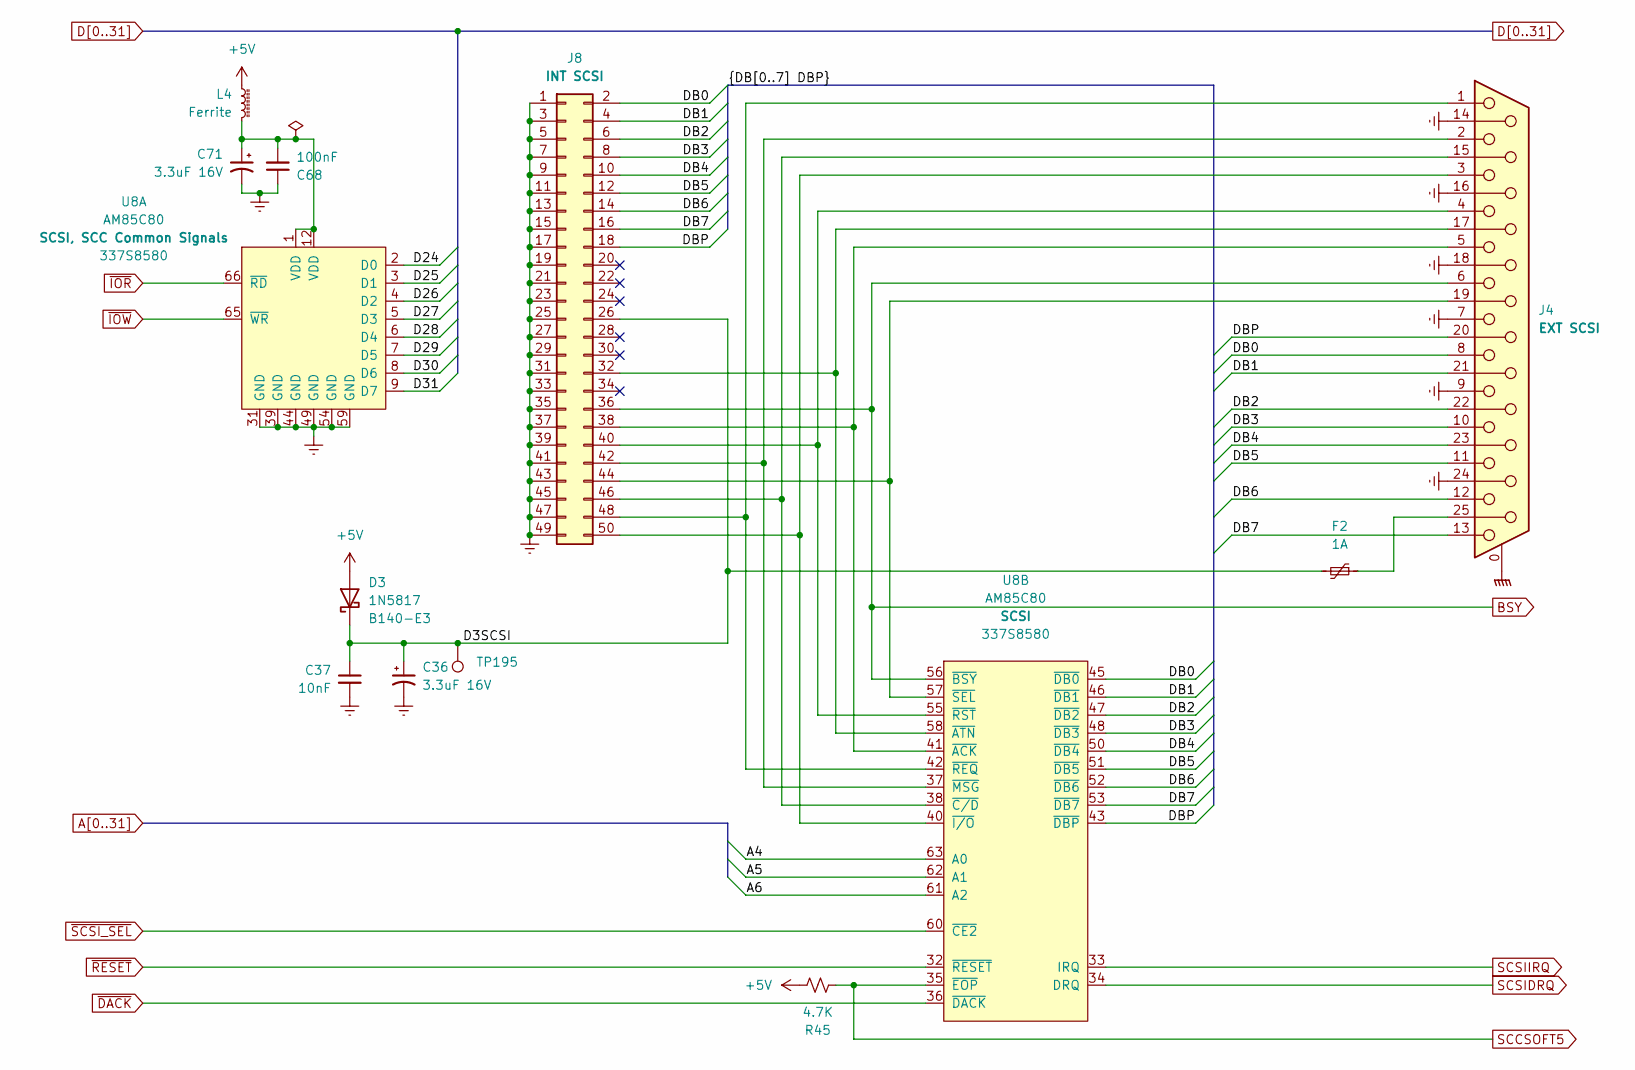
[picture p28: schematic scsi.kicad_sch]

Parts:
C36: 3.3uF 16V; CP_EIA-3528-21_Kemet-B_Pad3.0x2.35mm_HandSolder
C37: 10nF; SMD_0603_1608Metric_Pad1.52x1.02mm
C68: 100nF; SMD_0603_1608Metric_Pad1.52x1.02mm
C71: 3.3uF 16V; CP_EIA-3528-12_Kemet-T_Pad1.98x2.35mm_HandSolder
D3: 1N5817; D_SMA; PartNum B140-E3
F2: 1A; Fuse_2512_6332Metric_Pad2.54x2.54mm_HandSolder
J4: EXT SCSI; DSUB-25_Socket_Horizontal_P2.77x2.84mm_EdgePinOffset7.70mm_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
J8: INT SCSI; IDC-Header_2x25_P2.54mm_Vertical
L4: Ferrite; L_2010_5025Metric_Pad2.0x2.2mm_HandSolder
R45: 4.7K; SMD_0805_2012Metric_Pad1.25x1.65mm
TP195: TestPoint_THTPad_D1.0mm_Drill0.5mm
U8: AM85C80; PLCC-68_24.2x24.2mm_P1.27mm_oval; PartNum 337S8580

Connections:
+5V: D3.2 (A), L4.2, R45.1
A4: U8.63 (A0)
A5: U8.62 (A1)
A6: U8.61 (A2)
BSY: J4.6, J8.36, U8.56 (~BSY)
D3SCSI: C36.1, C37.1, D3.1 (K), F2.2, J8.26, TP195.1
D24: U8.2 (D0)
D25: U8.3 (D1)
D26: U8.4 (D2)
D27: U8.5 (D3)
D28: U8.6 (D4)
D29: U8.7 (D5)
D30: U8.8 (D6)
D31: U8.9 (D7)
DB0: J4.8, J8.2, U8.45 (~DB0)
DB1: J4.21, J8.4, U8.46 (~DB1)
DB2: J4.22, J8.6, U8.47 (~DB2)
DB3: J4.10, J8.8, U8.48 (~DB3)
DB4: J4.23, J8.10, U8.50 (~DB4)
DB5: J4.11, J8.12, U8.51 (~DB5)
DB6: J4.12, J8.14, U8.52 (~DB6)
DB7: J4.13, J8.16, U8.53 (~DB7)
DBP: J4.20, J8.18, U8.43 (~DBP)
GND: C36.2, C37.2, C68.1, C71.2, J4.7, J4.9, J4.14, J4.16, J4.18, J4.24, J8.1, J8.3, J8.5, J8.7, J8.9, J8.11, J8.13, J8.15, J8.17, J8.19, J8.21, J8.23, J8.25, J8.27, J8.29, J8.31, J8.33, J8.35, J8.37, J8.39, J8.41, J8.43, J8.45, J8.47, J8.49, U8.31 (GND), U8.39 (GND), U8.44 (GND), U8.49 (GND), U8.54 (GND), U8.59 (GND)
GNDPWR: J4.0 (PAD)
unnamed: C68.2, C71.1, L4.1, U8.1 (VDD), U8.12 (VDD)
unnamed: F2.1, J4.25
unnamed: J4.1, J8.48, U8.42 (~REQ)
unnamed: J4.2, J8.42, U8.37 (~MSG)
unnamed: J4.3, J8.50, U8.40 (~I/O)
unnamed: J4.4, J8.40, U8.55 (~RST)
unnamed: J4.5, J8.38, U8.41 (~ACK)
unnamed: J4.15, J8.46, U8.38 (~C/D)
unnamed: J4.17, J8.32, U8.58 (~ATN)
unnamed: J4.19, J8.44, U8.57 (~SEL)
SCCSOFT5: R45.2, U8.35 (~EOP)
SCSIDRQ: U8.34 (DRQ)
SCSIIRQ: U8.33 (IRQ)
~DACK: U8.36 (~DACK)
~IOR: U8.66 (~RD)
~IOW: U8.65 (~WR)
~RESET: U8.32 (~RESET)
~SCSI_SEL: U8.60 (~CE2)
