btb/ClassicII/ClassicIIRevB/serial.kicad_sch

## KiCad design ClassicIIRevB/serial.kicad_sch (2026-08-08)

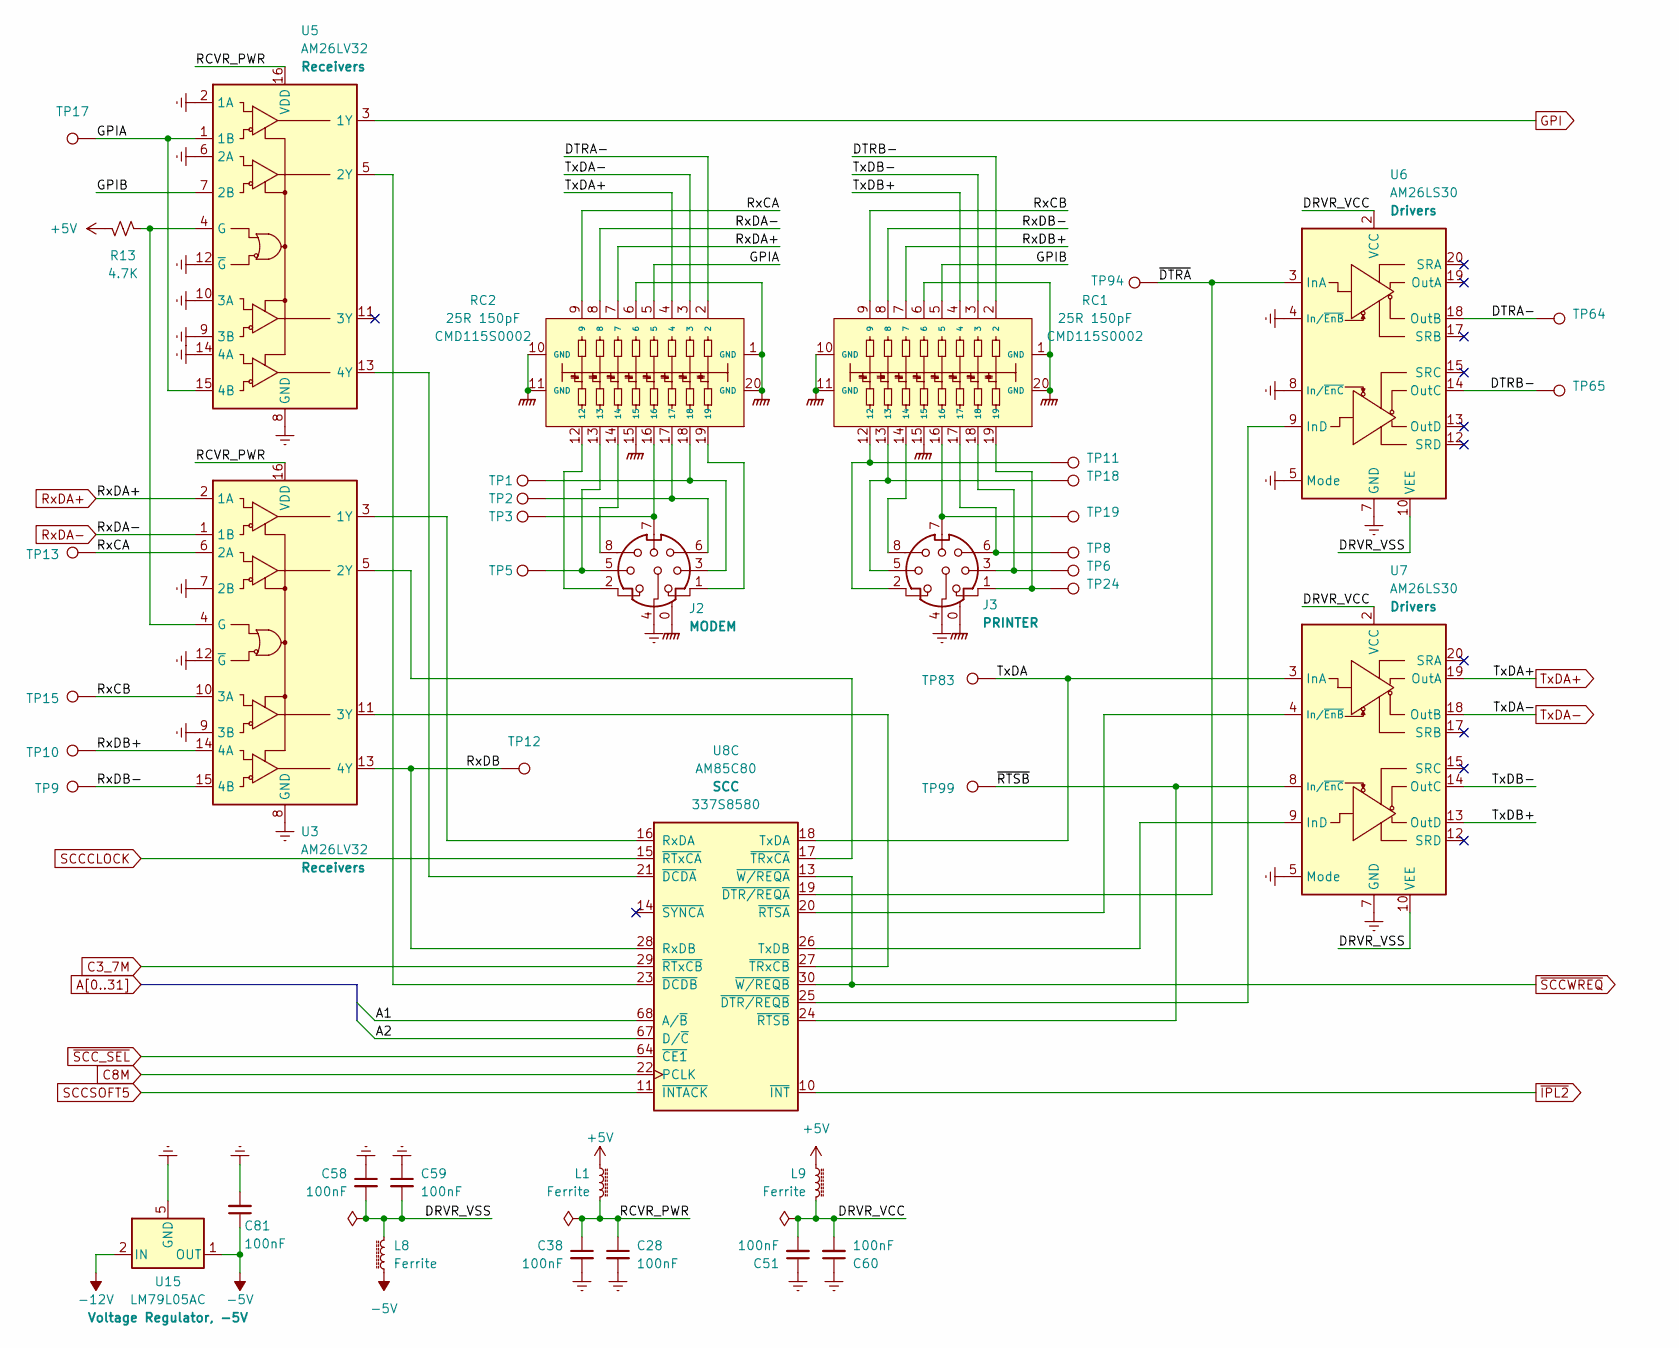
[picture p29: schematic serial.kicad_sch]

Parts:
C28, C38, C51, C58, C59, C60, C81: 100nF; SMD_0603_1608Metric_Pad1.52x1.02mm
J2: MODEM; TE_5749268-1_MINI_DIN_8_RA_Shield
J3: PRINTER; TE_5749268-1_MINI_DIN_8_RA_Shield
L1, L8, L9: Ferrite; L_2010_5025Metric_Pad2.0x2.2mm_HandSolder
R13: 4.7K; SMD_0805_2012Metric_Pad1.25x1.65mm
RC1, RC2: 25R 150pF; SOIC-20W_7.5x12.8mm_P1.27mm_RC; PartNum CMD115S0002
TP1, TP2, TP3, TP5, TP6, TP8, TP9, TP10, TP11, TP12, TP18, TP19, TP24, TP64, TP65, TP83, TP94, TP99: TestPoint_THTPad_D1.0mm_Drill0.5mm
TP13, TP15, TP17: TestPoint_Pad_D1.0mm
U3, U5: AM26LV32; SOIC-16_4.55x10.3mm_P1.27mm_oval
U6, U7: AM26LS30; PLCC-20_rounded
U8: AM85C80; PLCC-68_24.2x24.2mm_P1.27mm_oval; PartNum 337S8580
U15: LM79L05AC; SOIC-8_3.9x4.9mm_P1.27mm_oval

Connections:
+5V: L1.2, L9.2, R13.1
-5V: C81.1, L8.2, U15.1 (OUT)
-12V: U15.2 (IN), U15.3 (IN), U15.6 (IN), U15.7 (IN)
A1: U8.68 (A/~B)
A2: U8.67 (D/~C)
C3_7M: U8.29 (~RTxCB)
C8M: U8.22 (PCLK)
DRVR_VCC: C51.2, C60.2, L9.1, U6.2 (VCC), U7.2 (VCC)
DRVR_VSS: C58.2, C59.2, L8.1, U6.10 (VEE), U7.10 (VEE)
DTRA-: RC2.2, TP64.1, U6.18 (OutB)
DTRB-: RC1.2, TP65.1, U6.14 (OutC)
GND: C28.2, C38.2, C51.1, C58.1, C59.1, C60.1, C81.2, J2.4, J3.4, U3.7 (2B), U3.8 (GND), U3.9 (3B), U3.12 (~G), U5.2 (1A), U5.6 (2A), U5.8 (GND), U5.9 (3B), U5.10 (3A), U5.12 (~G), U5.14 (4A), U6.4 (In/~EnB), U6.5 (Mode), U6.7 (GND), U6.8 (In/~EnC), U7.5 (Mode), U7.7 (GND), U15.5 (GND)
GNDPWR: J2.0, J3.0, RC1.1 (GND), RC1.6, RC1.10 (GND), RC1.11 (GND), RC1.15, RC1.20 (GND), RC2.1 (GND), RC2.6, RC2.10 (GND), RC2.11 (GND), RC2.15, RC2.20 (GND)
GPI: U5.3 (1Y)
GPIA: RC2.5, TP17.1, U5.1 (1B), U5.15 (4B)
GPIB: RC1.5, U5.7 (2B)
unnamed: J2.1, RC2.19
unnamed: J2.2, RC2.12
unnamed: J2.3, RC2.18, TP1.1
unnamed: J2.5, RC2.13, TP5.1
unnamed: J2.6, RC2.17, TP2.1
unnamed: J2.7, RC2.16, TP3.1
unnamed: J2.8, RC2.14
unnamed: J3.1, RC1.19, TP24.1
unnamed: J3.2, RC1.12, TP11.1
unnamed: J3.3, RC1.18, TP6.1
unnamed: J3.5, RC1.13, TP18.1
unnamed: J3.6, RC1.17, TP8.1
unnamed: J3.7, RC1.16, TP19.1
unnamed: J3.8, RC1.14
unnamed: R13.2, U3.4 (G), U5.4 (G)
unnamed: U3.3 (1Y), U8.16 (RxDA)
unnamed: U3.5 (2Y), U8.17 (~TRxCA)
unnamed: U3.11 (3Y), U8.27 (~TRxCB)
unnamed: U5.5 (2Y), U8.23 (~DCDB)
unnamed: U5.13 (4Y), U8.21 (~DCDA)
unnamed: U6.9 (InD), U8.25 (~DTR/REQB)
unnamed: U7.4 (In/~EnB), U8.20 (~RTSA)
unnamed: U7.9 (InD), U8.26 (TxDB)
RCVR_PWR: C28.1, C38.1, L1.1, U3.16 (VDD), U5.16 (VDD)
RxCA: RC2.9, TP13.1, U3.6 (2A)
RxCB: RC1.9, TP15.1, U3.10 (3A)
RxDA+: RC2.7, U3.2 (1A)
RxDA-: RC2.8, U3.1 (1B)
RxDB: TP12.1, U3.13 (4Y), U8.28 (RxDB)
RxDB+: RC1.7, TP10.1, U3.14 (4A)
RxDB-: RC1.8, TP9.1, U3.15 (4B)
SCCCLOCK: U8.15 (~RTxCA)
SCCSOFT5: U8.11 (~INTACK)
TxDA: TP83.1, U7.3 (InA), U8.18 (TxDA)
TxDA+: RC2.4, U7.19 (OutA)
TxDA-: RC2.3, U7.18 (OutB)
TxDB+: RC1.4, U7.13 (OutD)
TxDB-: RC1.3, U7.14 (OutC)
~DTRA: TP94.1, U6.3 (InA), U8.19 (~DTR/REQA)
~IPL2: U8.10 (~INT)
~RTSB: TP99.1, U7.8 (In/~EnC), U8.24 (~RTSB)
~SCCWREQ: U8.13 (~W/REQA), U8.30 (~W/REQB)
~SCC_SEL: U8.64 (~CE1)
