btb/ClassicII/ClassicIIRevB/simm.kicad_sch

## KiCad design ClassicIIRevB/simm.kicad_sch (2026-08-08)

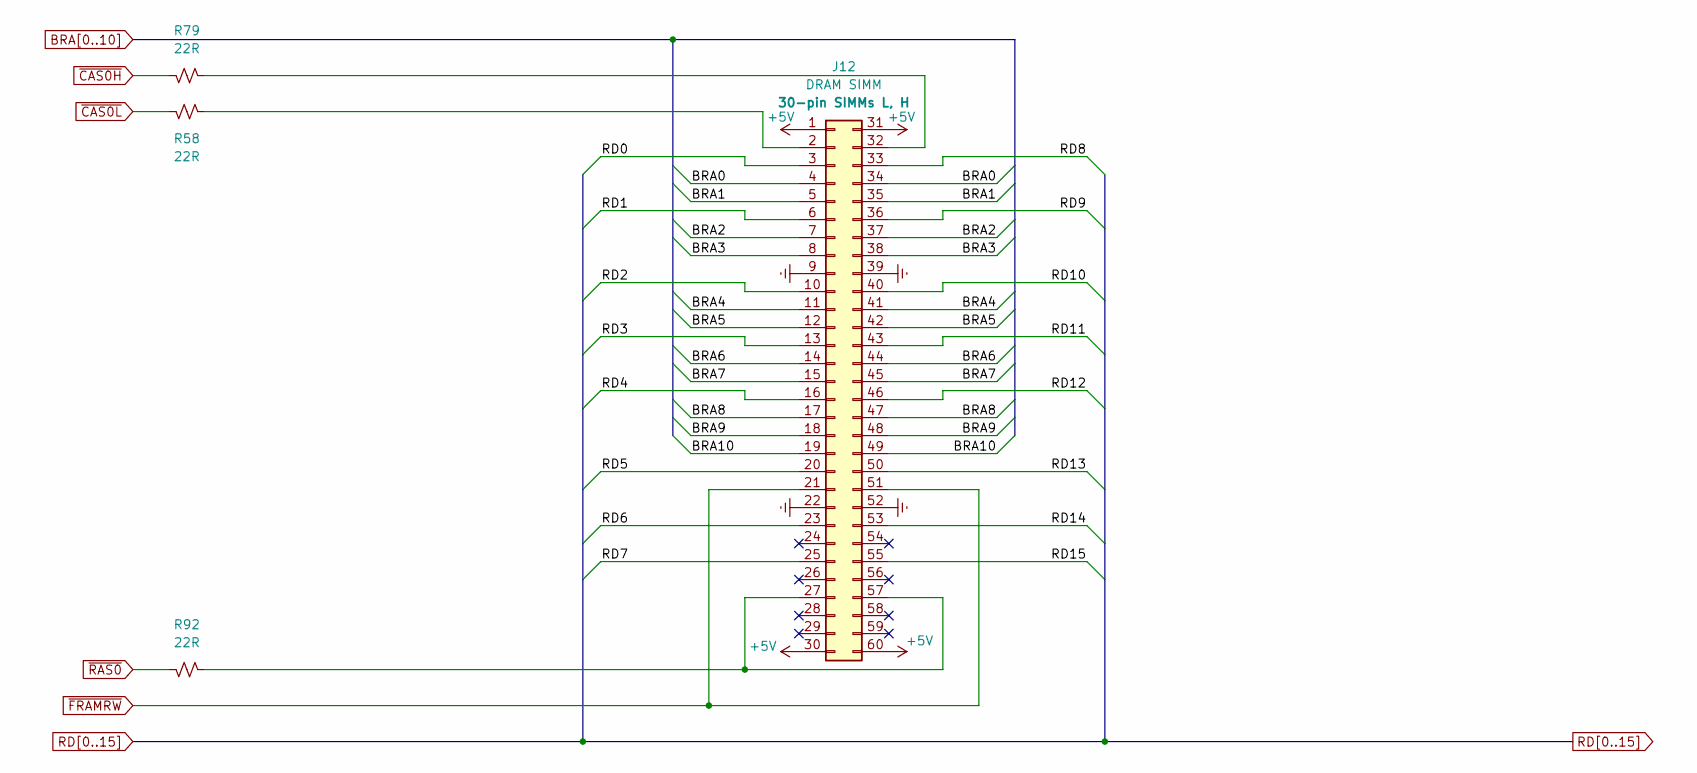
[picture p30: schematic simm.kicad_sch]

Parts:
J12: DRAM SIMM; SIMMSocket_2x30_angled
R58, R79, R92: 22R; SMD_0805_2012Metric_Pad1.25x1.65mm

Connections:
+5V: J12.1, J12.30, J12.31, J12.60
BRA0: J12.4, J12.34
BRA1: J12.5, J12.35
BRA2: J12.7, J12.37
BRA3: J12.8, J12.38
BRA4: J12.11, J12.41
BRA5: J12.12, J12.42
BRA6: J12.14, J12.44
BRA7: J12.15, J12.45
BRA8: J12.17, J12.47
BRA9: J12.18, J12.48
BRA10: J12.19, J12.49
GND: J12.9, J12.22, J12.39, J12.52
unnamed: J12.2, R58.2
unnamed: J12.27, J12.57, R92.1
unnamed: J12.32, R79.2
RD0: J12.3
RD1: J12.6
RD2: J12.10
RD3: J12.13
RD4: J12.16
RD5: J12.20
RD6: J12.23
RD7: J12.25
RD8: J12.33
RD9: J12.36
RD10: J12.40
RD11: J12.43
RD12: J12.46
RD13: J12.50
RD14: J12.53
RD15: J12.55
~CAS0H: R79.1
~CAS0L: R58.1
~FRAMRW: J12.21, J12.51
~RAS0: R92.2
