btb/ClassicII/ClassicIIRevB/sound.kicad_sch

## KiCad design ClassicIIRevB/sound.kicad_sch (2026-08-08)

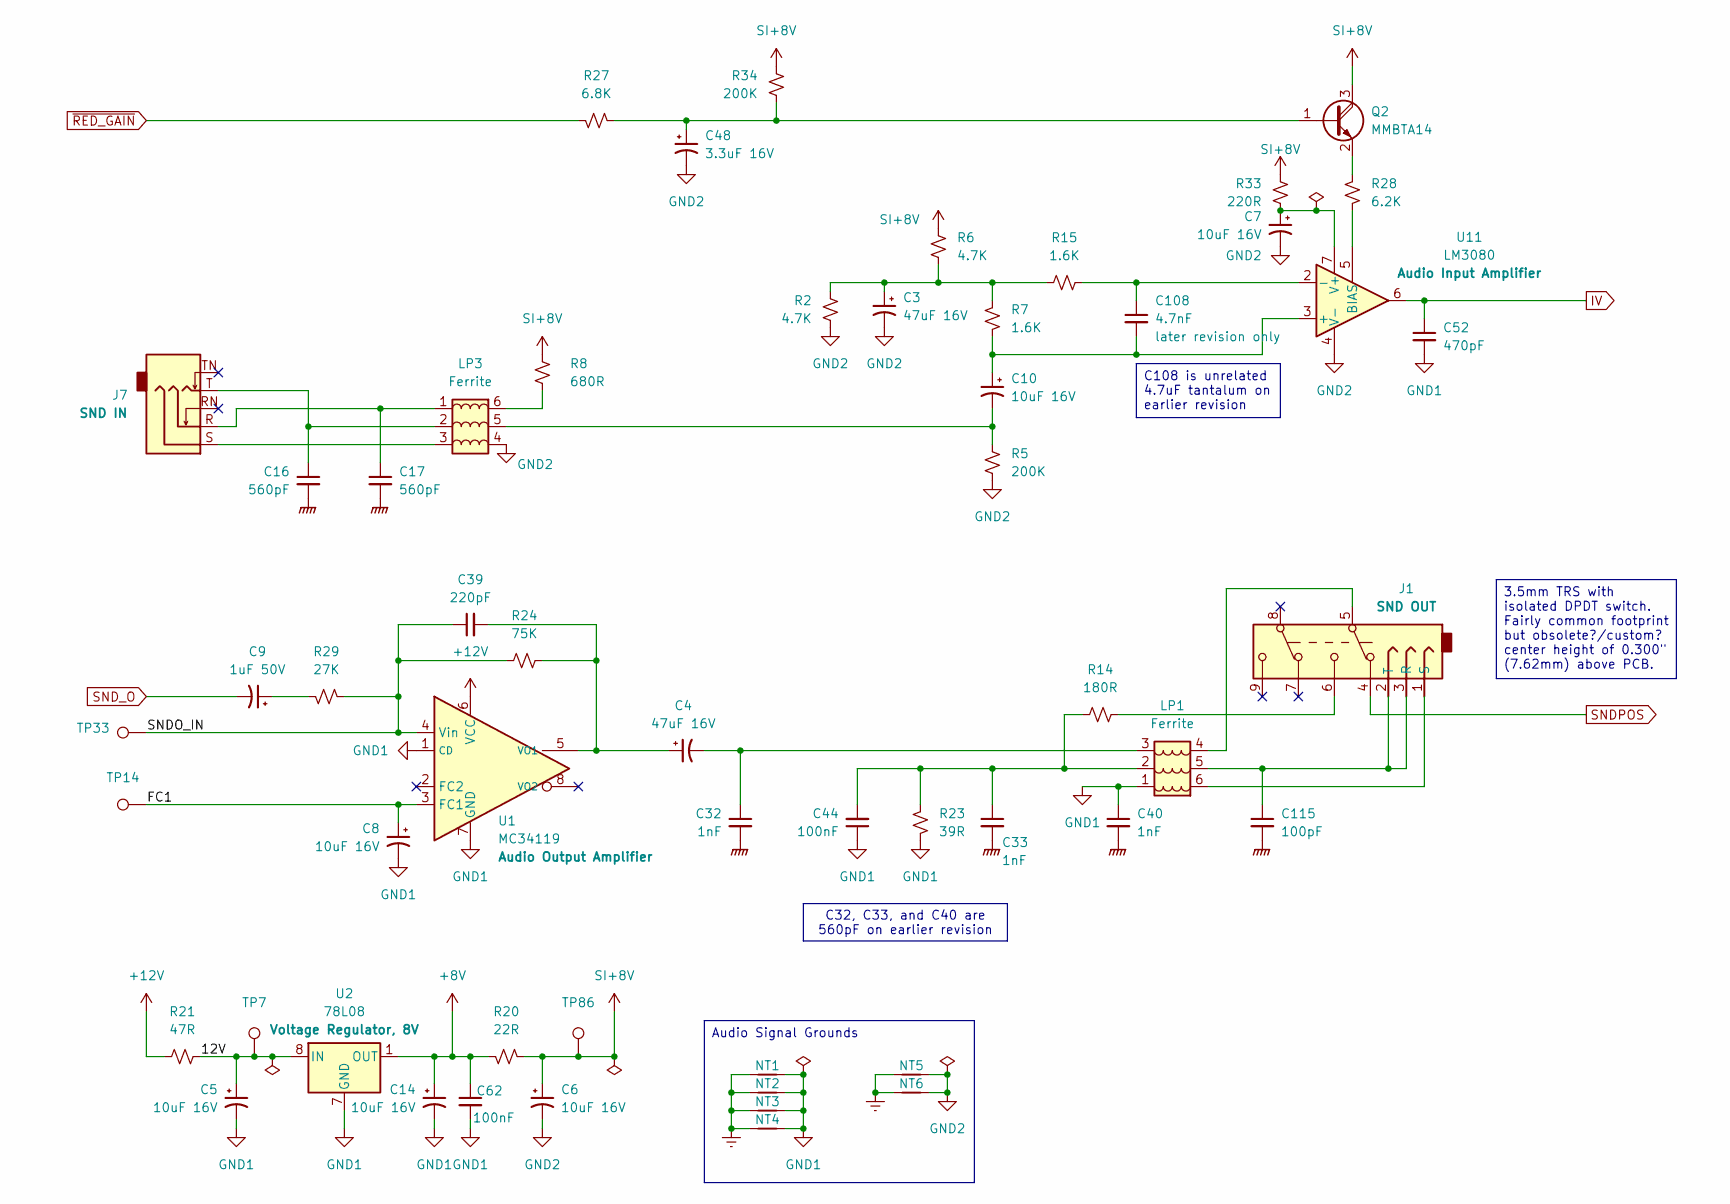
[picture p31: schematic sound.kicad_sch]

Parts:
C3, C4: 47uF 16V; CP_Elec_6.3x5.4
C5, C6, C7, C8, C10, C14: 10uF 16V; CP_Elec_4x5.8
C9: 1uF 50V; CP_Elec_4x5.8
C16, C17: 560pF; SMD_0603_1608Metric_Pad1.52x1.02mm
C32, C33, C40: 1nF; SMD_0603_1608Metric_Pad1.52x1.02mm
C39: 220pF; SMD_0603_1608Metric_Pad1.52x1.02mm
C44, C62: 100nF; SMD_0603_1608Metric_Pad1.52x1.02mm
C48: 3.3uF 16V; CP_EIA-3528-21_Kemet-B_Pad3.0x2.35mm_HandSolder
C52: 470pF; SMD_0603_1608Metric_Pad1.52x1.02mm
C108: 4.7nF; SMD_0603_1608Metric_Pad1.52x1.02mm
C115: 100pF; SMD_0603_1608Metric_Pad1.52x1.02mm
J1: SND OUT; Jack_3.5mm_SameSky_SJ3589ANG
J7: SND IN; Jack_3.5mm_CUI_SJ1-3535NG_Horizontal
LP1, LP3: Ferrite; L_Pack03_P2.54mm
NT1, NT2, NT3, NT4, NT5, NT6: NetTie_2; NetTie-2_THT_Pad0.43mm
Q2: MMBTA14; SOT-23_Handsoldering
R2, R6: 4.7K; SMD_0805_2012Metric_Pad1.25x1.65mm
R5, R34: 200K; SMD_0805_2012Metric_Pad1.25x1.65mm
R7, R15: 1.6K; SMD_0805_2012Metric_Pad1.25x1.65mm
R8: 680R; SMD_0805_2012Metric_Pad1.25x1.65mm
R14: 180R; SMD_0805_2012Metric_Pad1.25x1.65mm
R20: 22R; SMD_0805_2012Metric_Pad1.25x1.65mm
R21: 47R; SMD_0805_2012Metric_Pad1.25x1.65mm
R23: 39R; SMD_0805_2012Metric_Pad1.25x1.65mm
R24: 75K; SMD_0805_2012Metric_Pad1.25x1.65mm
R27: 6.8K; SMD_0805_2012Metric_Pad1.25x1.65mm
R28: 6.2K; SMD_0805_2012Metric_Pad1.25x1.65mm
R29: 27K; SMD_0805_2012Metric_Pad1.25x1.65mm
R33: 220R; SMD_0805_2012Metric_Pad1.25x1.65mm
TP7, TP33, TP86: TestPoint_THTPad_D1.0mm_Drill0.5mm
TP14: TestPoint_Pad_D1.0mm
U1: MC34119; SOIC-8_3.9x4.9mm_P1.27mm_oval
U2: 78L08; SOIC-8_3.9x4.9mm_P1.27mm_oval
U11: LM3080; SOIC-8_3.9x4.9mm_P1.27mm_oval

Connections:
12V: C5.1, R21.1, TP7.1, U2.8 (IN)
+8V: C14.1, C62.1, R20.1, U2.1 (OUT)
+12V: R21.2, U1.6 (VCC)
FC1: C8.1, TP14.1, U1.3 (FC1)
GND: NT1.2, NT2.2, NT3.2, NT4.2, NT5.2, NT6.2
GND1: C5.2, C8.2, C14.2, C40.1, C44.1, C52.2, C62.2, LP1.1, NT1.1, NT2.1, NT3.1, NT4.1, R23.2, U1.1 (CD), U1.7 (GND), U2.2 (GND), U2.3 (GND), U2.6 (GND), U2.7 (GND)
GND2: C3.2, C6.2, C7.2, C48.2, LP3.4, NT5.1, NT6.1, R2.1, R5.2, U11.4 (V-)
GNDPWR: C16.2, C17.2, C32.2, C33.2, C40.2, C115.2
IV: C52.1, U11.6
unnamed: C3.1, R2.2, R6.1, R7.1, R15.1
unnamed: C7.1, R33.1, U11.7 (V+)
unnamed: C9.1, R29.2
unnamed: C10.1, C108.2, R7.2, U11.3 (+)
unnamed: C10.2, LP3.5, R5.1
unnamed: C16.1, J7.T, LP3.2
unnamed: C17.1, J7.R, LP3.1
unnamed: C4.2, C32.1, LP1.3
unnamed: C33.1, C44.2, LP1.2, R14.1, R23.1
unnamed: C4.1, C39.2, R24.2, U1.5 (VO1)
unnamed: C48.1, Q2.1 (B), R27.2, R34.1
unnamed: C108.1, R15.2, U11.2 (-)
unnamed: C115.1, J1.2 (T), J1.3 (R), LP1.5
unnamed: J1.1 (S), LP1.6
unnamed: J1.5, LP1.4
unnamed: J1.6, R14.2
unnamed: J7.S, LP3.3
unnamed: LP3.6, R8.1
unnamed: Q2.2 (E), R28.1
unnamed: R28.2, U11.5 (BIAS)
SI+8V: C6.1, Q2.3 (C), R6.2, R8.2, R20.2, R33.2, R34.2, TP86.1
SNDO_IN: C39.1, R24.1, R29.1, TP33.1, U1.4 (Vin)
SNDPOS: J1.4
SND_O: C9.2
~RED_GAIN: R27.1

Notes on the sheet:
C108 is unrelated 4.7uF tantalum on earlier revision
Audio Signal Grounds
3.5mm TRS with isolated DPDT switch. Fairly common footprint but obsolete?/custom? center height of 0.300" (7.62mm) above PCB.
C32, C33, and C40 are 560pF on earlier revision
