btb/ClassicII/ClassicIIRevB/test.kicad_sch

## KiCad design ClassicIIRevB/test.kicad_sch (2026-08-08)

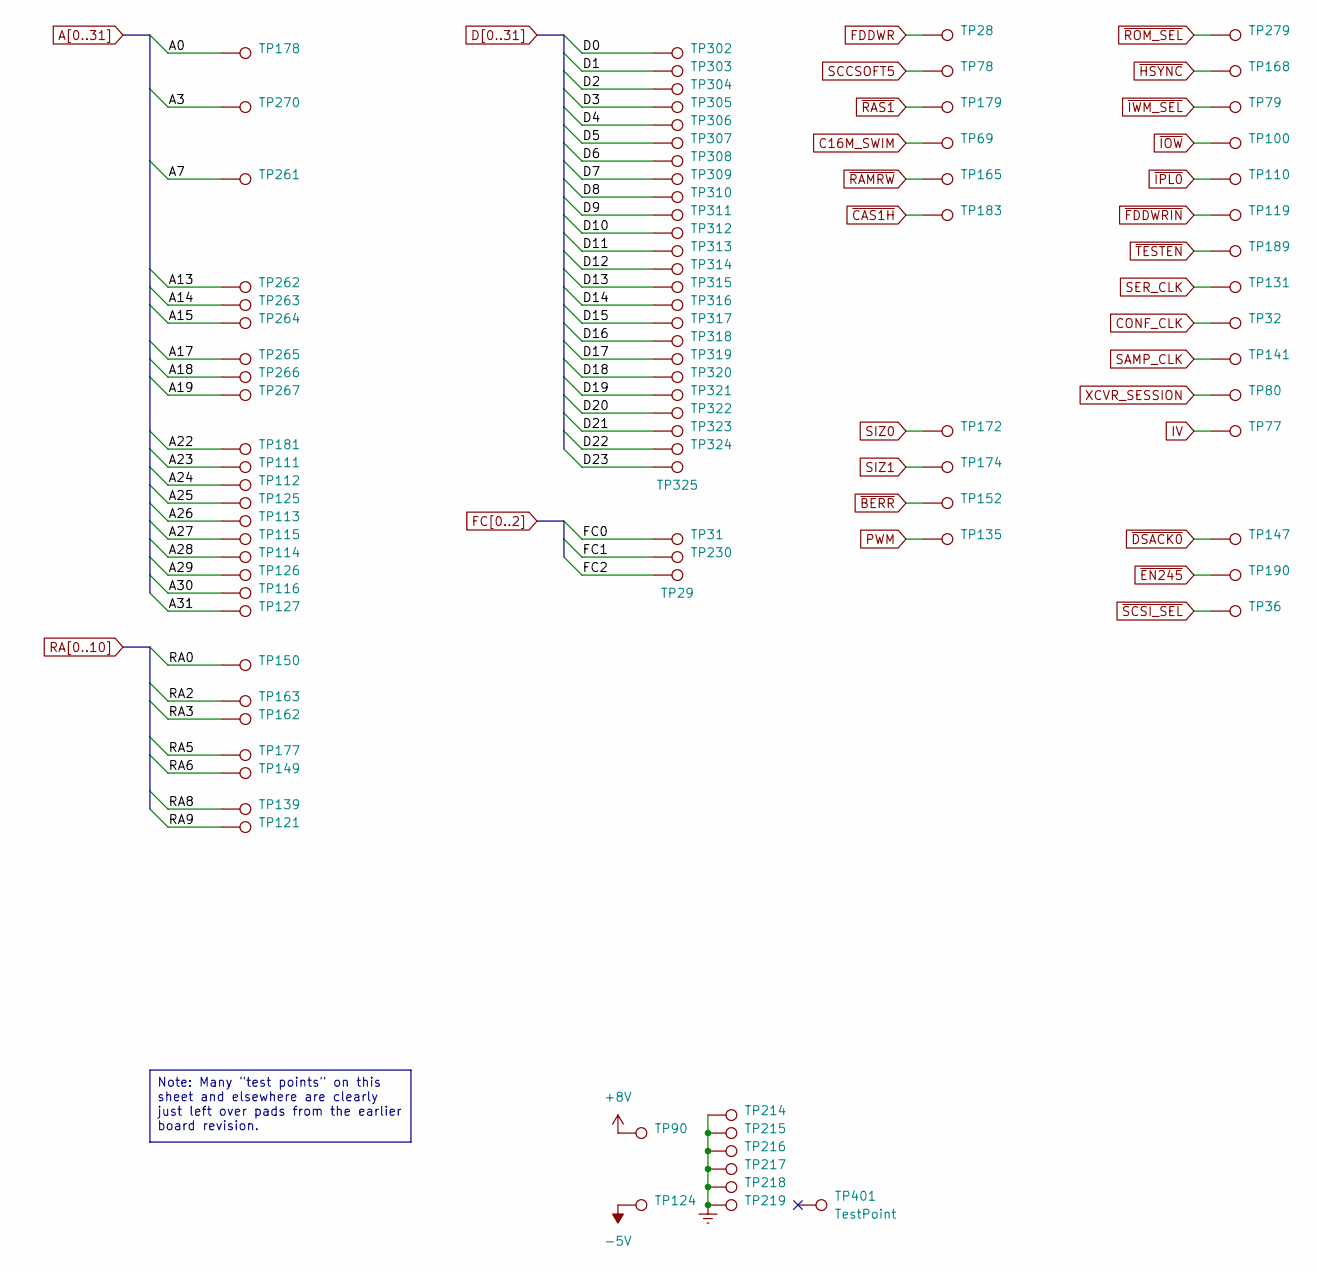
[picture p32: schematic test.kicad_sch]

Parts:
TP28, TP69, TP78, TP135, TP149, TP150, TP152, TP162, TP163, TP165, TP172, TP174, TP177, TP178, TP179, TP181, TP183, TP230: TestPoint_Pad_D1.0mm
TP29, TP31, TP32, TP36, TP77, TP79, TP80, TP90, TP100, TP110, TP111, TP112, TP113, TP114, TP115, TP116, TP119, TP121, TP124, TP125, TP126, TP127, TP131, TP139, TP141, TP147, TP168, TP189, TP190, TP214, TP215, TP216, TP217, TP218, TP219, TP261, TP262, TP263, TP264, TP265, TP266, TP267, TP270, TP279, TP302, TP303, TP304, TP305, TP306, TP307, TP308, TP309, TP310, TP311, TP312, TP313, TP314, TP315, TP316, TP317, TP318, TP319, TP320, TP321, TP322, TP323, TP324, TP325: TestPoint_THTPad_D1.0mm_Drill0.5mm
TP401: TestPoint; TestPoint_Pad_1.5x1.5mm

Connections:
+8V: TP90.1
-5V: TP124.1
A0: TP178.1
A3: TP270.1
A7: TP261.1
A13: TP262.1
A14: TP263.1
A15: TP264.1
A17: TP265.1
A18: TP266.1
A19: TP267.1
A22: TP181.1
A23: TP111.1
A24: TP112.1
A25: TP125.1
A26: TP113.1
A27: TP115.1
A28: TP114.1
A29: TP126.1
A30: TP116.1
A31: TP127.1
C16M_SWIM: TP69.1
CONF_CLK: TP32.1
D0: TP302.1
D1: TP303.1
D2: TP304.1
D3: TP305.1
D4: TP306.1
D5: TP307.1
D6: TP308.1
D7: TP309.1
D8: TP310.1
D9: TP311.1
D10: TP312.1
D11: TP313.1
D12: TP314.1
D13: TP315.1
D14: TP316.1
D15: TP317.1
D16: TP318.1
D17: TP319.1
D18: TP320.1
D19: TP321.1
D20: TP322.1
D21: TP323.1
D22: TP324.1
D23: TP325.1
FC0: TP31.1
FC1: TP230.1
FC2: TP29.1
FDDWR: TP28.1
GND: TP214.1, TP215.1, TP216.1, TP217.1, TP218.1, TP219.1
IV: TP77.1
PWM: TP135.1
RA0: TP150.1
RA2: TP163.1
RA3: TP162.1
RA5: TP177.1
RA6: TP149.1
RA8: TP139.1
RA9: TP121.1
SAMP_CLK: TP141.1
SCCSOFT5: TP78.1
SER_CLK: TP131.1
SIZ0: TP172.1
SIZ1: TP174.1
XCVR_SESSION: TP80.1
~BERR: TP152.1
~CAS1H: TP183.1
~DSACK0: TP147.1
~EN245: TP190.1
~FDDWRIN: TP119.1
~HSYNC: TP168.1
~IOW: TP100.1
~IPL0: TP110.1
~IWM_SEL: TP79.1
~RAMRW: TP165.1
~RAS1: TP179.1
~ROM_SEL: TP279.1
~SCSI_SEL: TP36.1
~TESTEN: TP189.1

Notes on the sheet:
Note: Many "test points" on this sheet and elsewhere are clearly just left over pads from the earlier board revision.
