btb/ClassicII/ClassicIIRevB/xcvr.kicad_sch

## KiCad design ClassicIIRevB/xcvr.kicad_sch (2026-08-08)

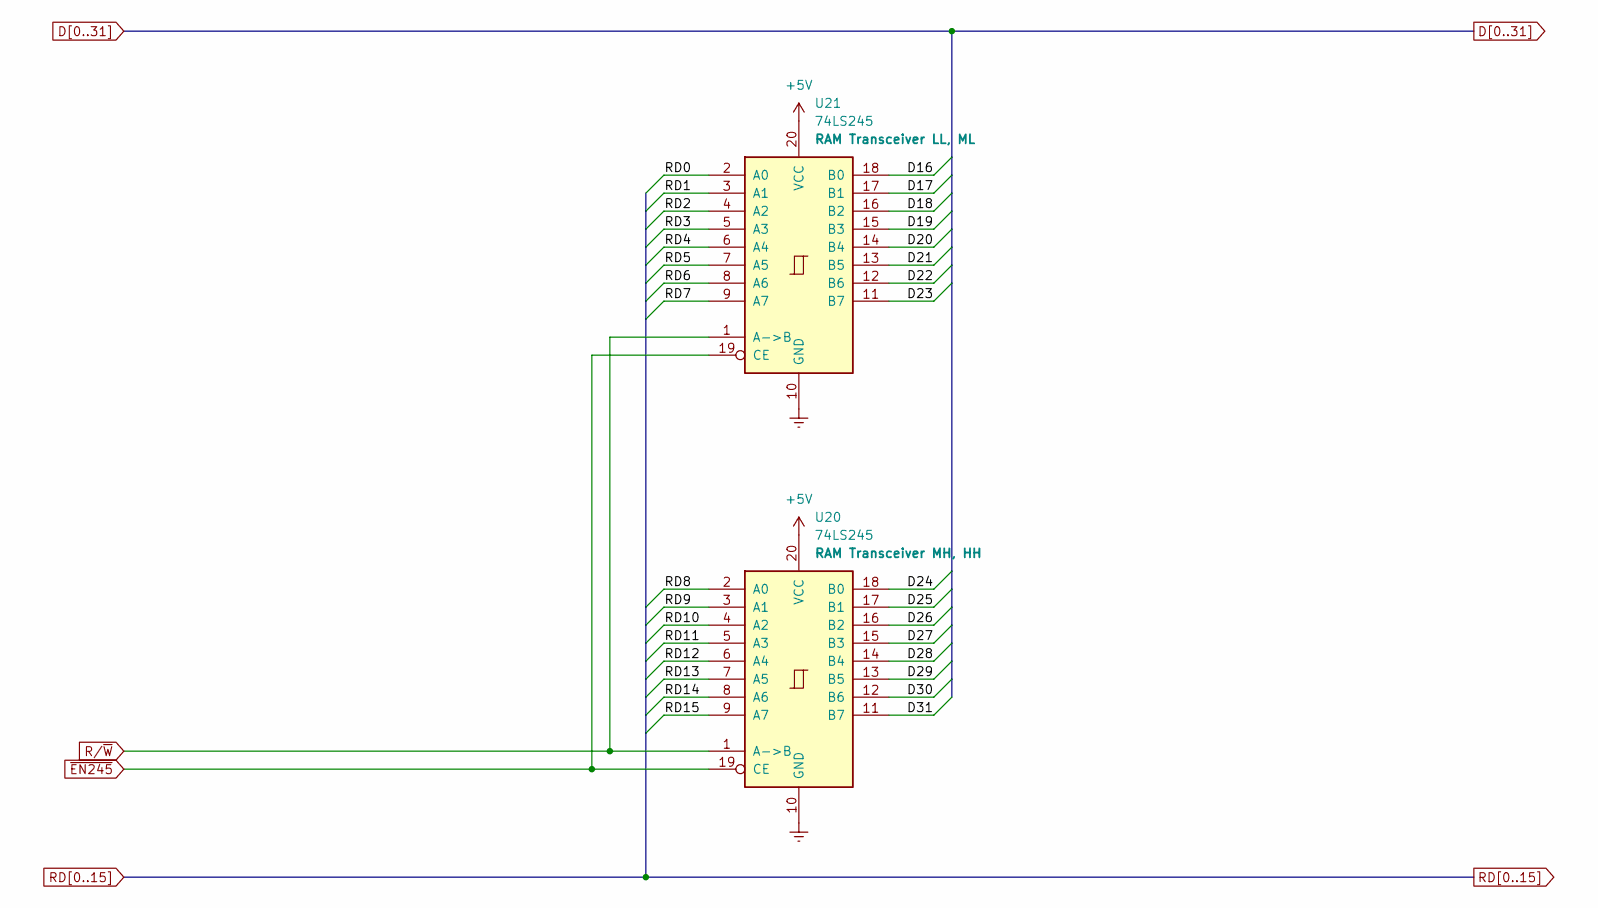
[picture p33: schematic xcvr.kicad_sch]

Parts:
U20, U21: 74LS245; SOIC-20W_7.5x12.8mm_P1.27mm_oval

Connections:
+5V: U20.20 (VCC), U21.20 (VCC)
D16: U21.18 (B0)
D17: U21.17 (B1)
D18: U21.16 (B2)
D19: U21.15 (B3)
D20: U21.14 (B4)
D21: U21.13 (B5)
D22: U21.12 (B6)
D23: U21.11 (B7)
D24: U20.18 (B0)
D25: U20.17 (B1)
D26: U20.16 (B2)
D27: U20.15 (B3)
D28: U20.14 (B4)
D29: U20.13 (B5)
D30: U20.12 (B6)
D31: U20.11 (B7)
GND: U20.10 (GND), U21.10 (GND)
RD0: U21.2 (A0)
RD1: U21.3 (A1)
RD2: U21.4 (A2)
RD3: U21.5 (A3)
RD4: U21.6 (A4)
RD5: U21.7 (A5)
RD6: U21.8 (A6)
RD7: U21.9 (A7)
RD8: U20.2 (A0)
RD9: U20.3 (A1)
RD10: U20.4 (A2)
RD11: U20.5 (A3)
RD12: U20.6 (A4)
RD13: U20.7 (A5)
RD14: U20.8 (A6)
RD15: U20.9 (A7)
R/~W: U20.1 (A->B), U21.1 (A->B)
~EN245: U20.19 (CE), U21.19 (CE)
